Pegmode/3D-Hologram---NAIT-CMPE2965/docs/cmpe2965 hologram presentation slides in person versionV2.pdf

# Table-Top Hologram Display

CMPE2965 CAPTONE PROJECT BY

DANIEL CHU, KADEN SPARROW

# Introduction

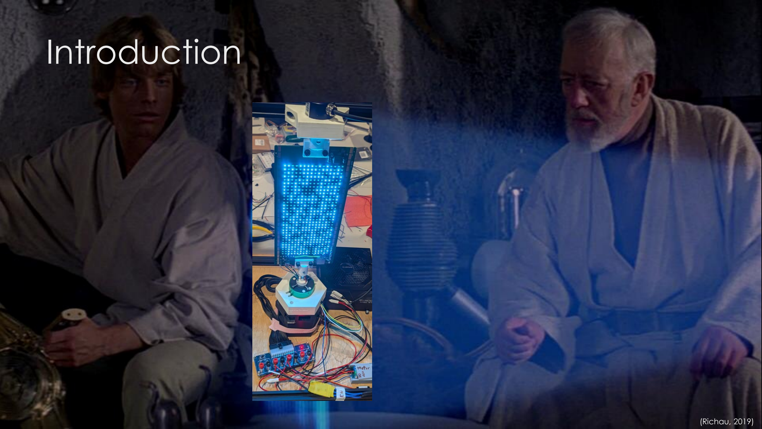
[picture p2: page 2]

(Richau, 2019)

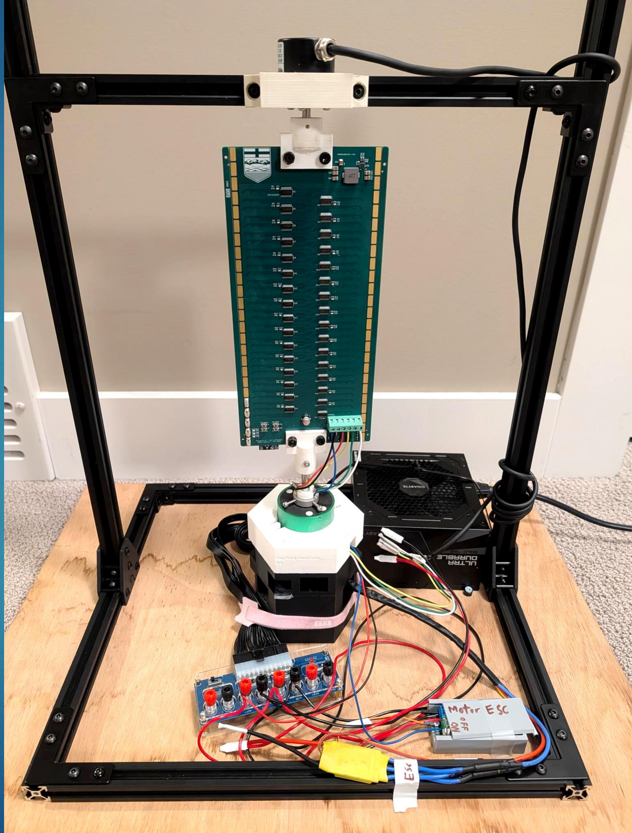
[picture p3: figure]

# Outline

- Embedded hardware
- Electro/Mechanical hardware
- Embedded software
- Server software
- Challenges
- Results

# Embedded Hardware Rotating

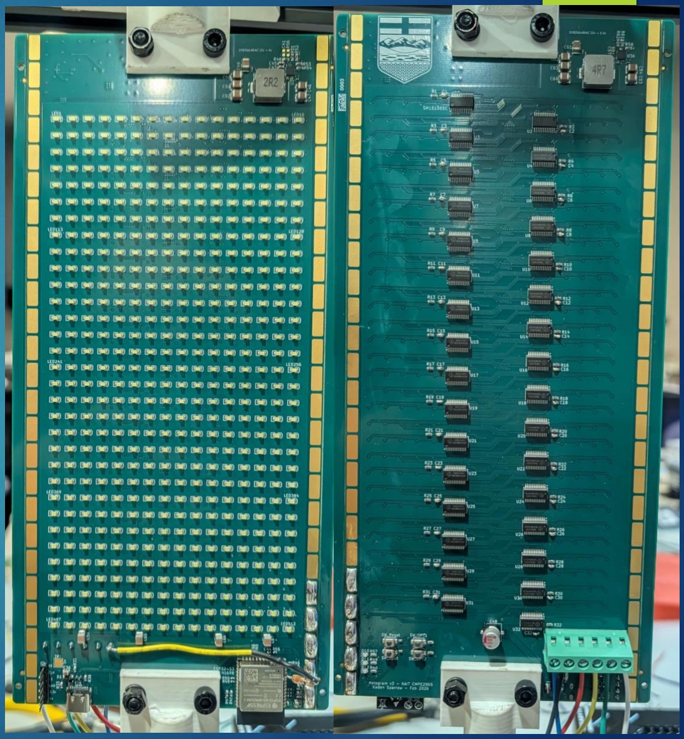
[picture p4: figure]

# Display PCB

- ESP32-S3-WROOM-1(N16R8)
- 32 x 16 LED array (512 total)
- Debug and brightness control buttons
- Debug LEDs (separate from array)
- Pads for soldering on counterweight
- Resettable fuse

# Electrical/Mechanical

# Components

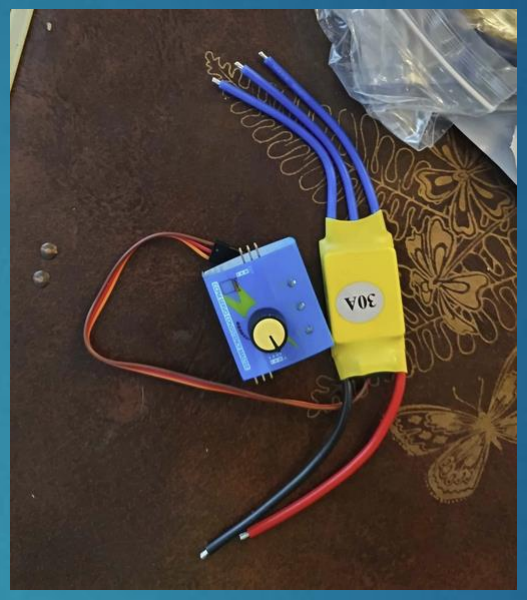
[picture p5: figure]
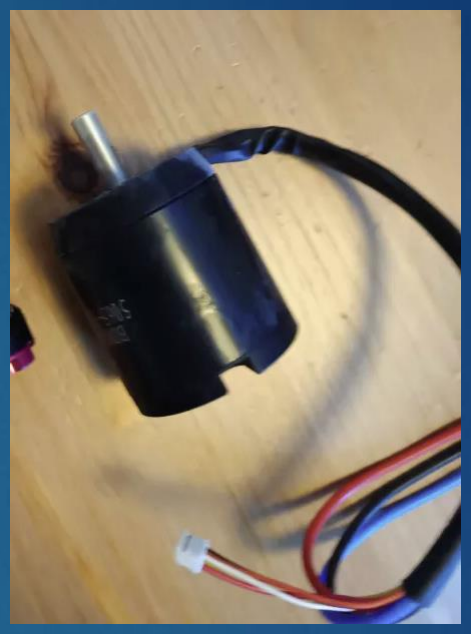
[picture p6: figure]

- 12V Electronic speed controller
- 330KV brushless motor
- 6-Wire slip ring
- Incremental rotary encoder

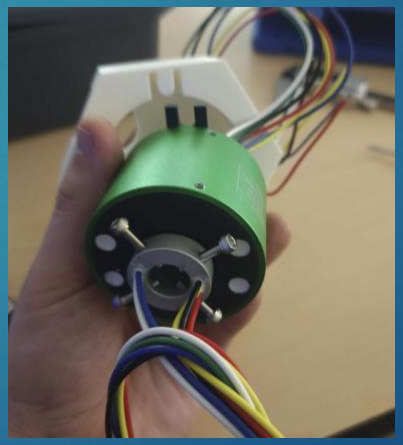
[picture p7: figure]
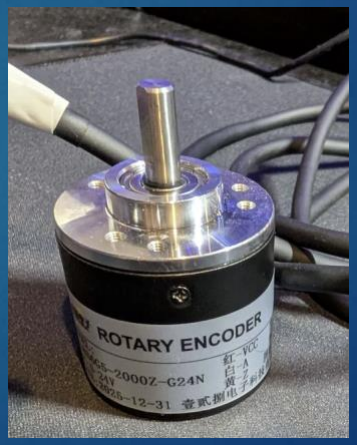
[picture p8: figure]

- Modular ATX power supply

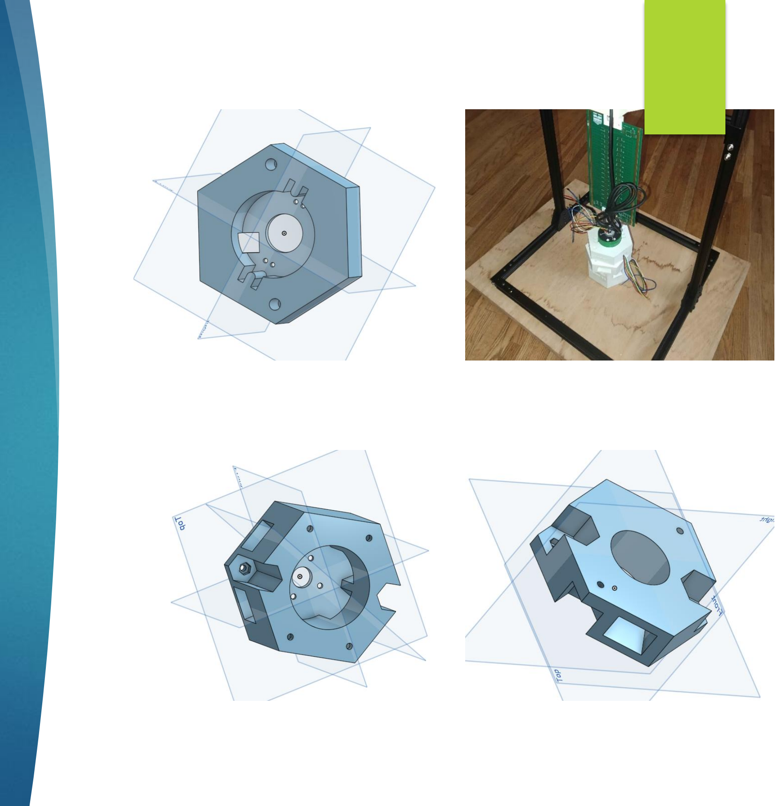
[picture p9: figure]

# Structural

# Components

- 3D printed parts to mount mechanical components
- 2020 T-Slot Aluminum
extrusions and a plywood
base as a structural frame
- All 3D printed components designed in Onshape

# Wireless control

- linear_index = (frame_index * slice_count) + slice_index;

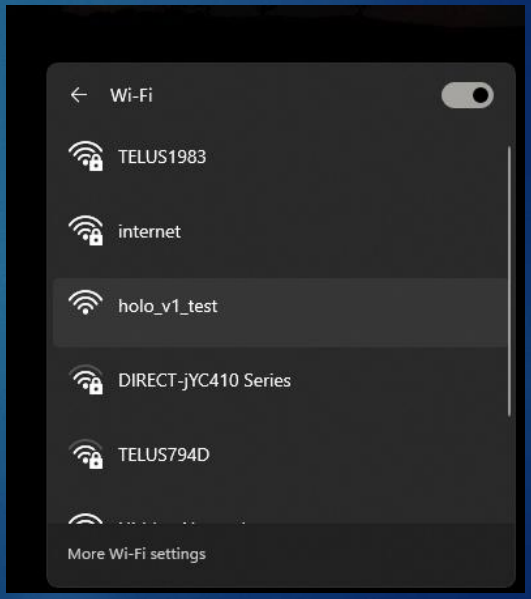
[picture p10: figure]
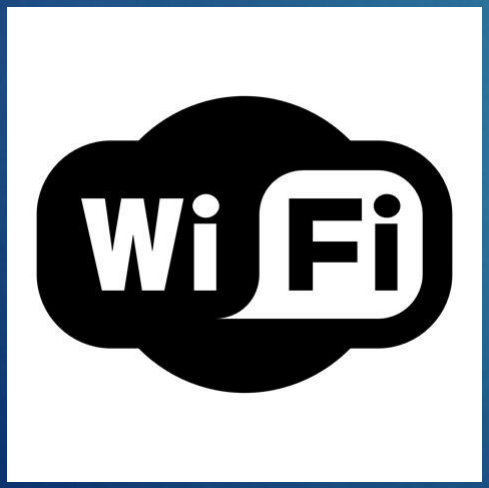
[picture p11: figure]
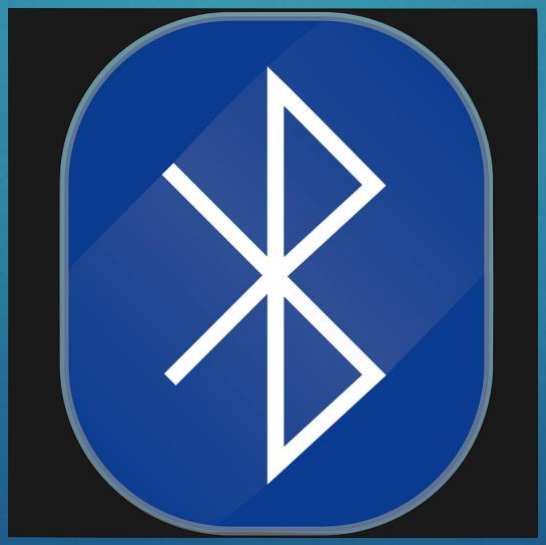
[picture p12: figure]

# Timing the Display

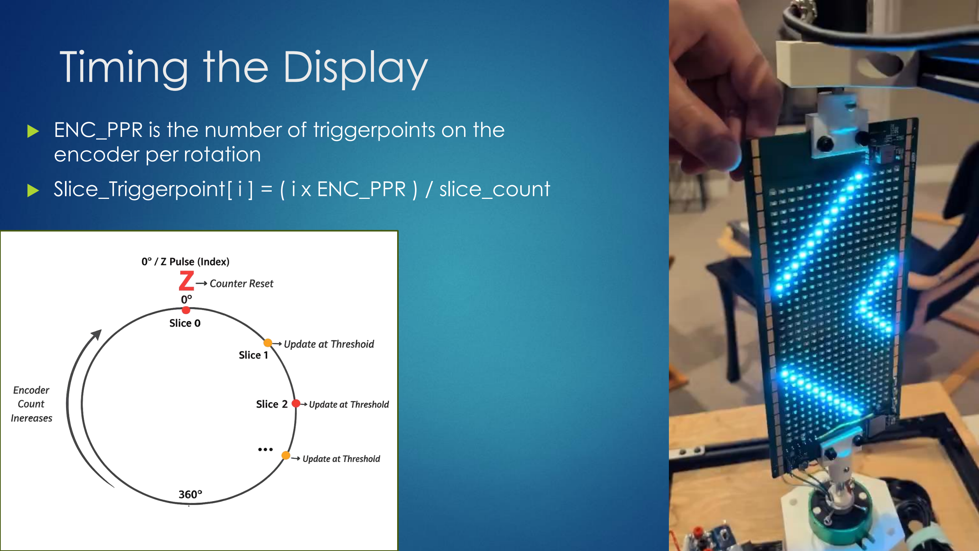
[picture p13: page 8]

- ENC_PPR is the number of triggerpoints on the encoder per rotation
- Slice_Triggerpoint[ i ] = ( i x ENC_PPR ) / slice_count

# Voxel Conversion Tool

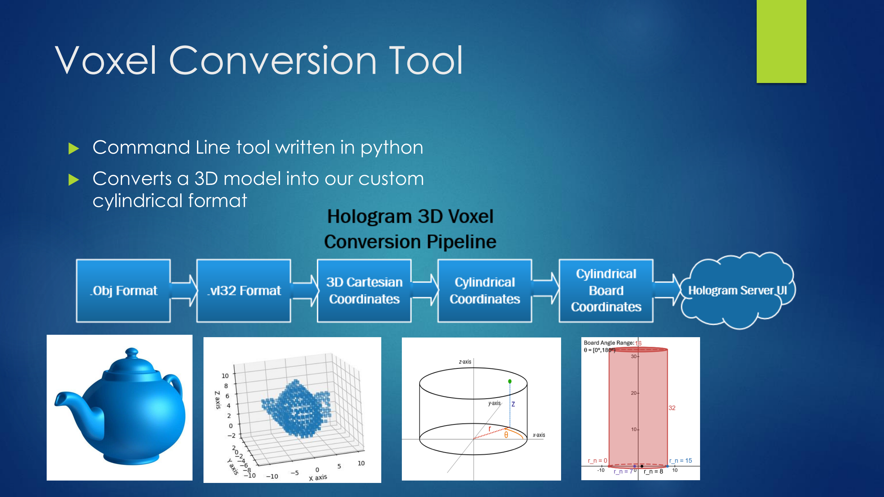
[picture p14: page 9]

- Command Line tool written in python
- Converts a 3D model into our custom cylindrical format

# Server UI

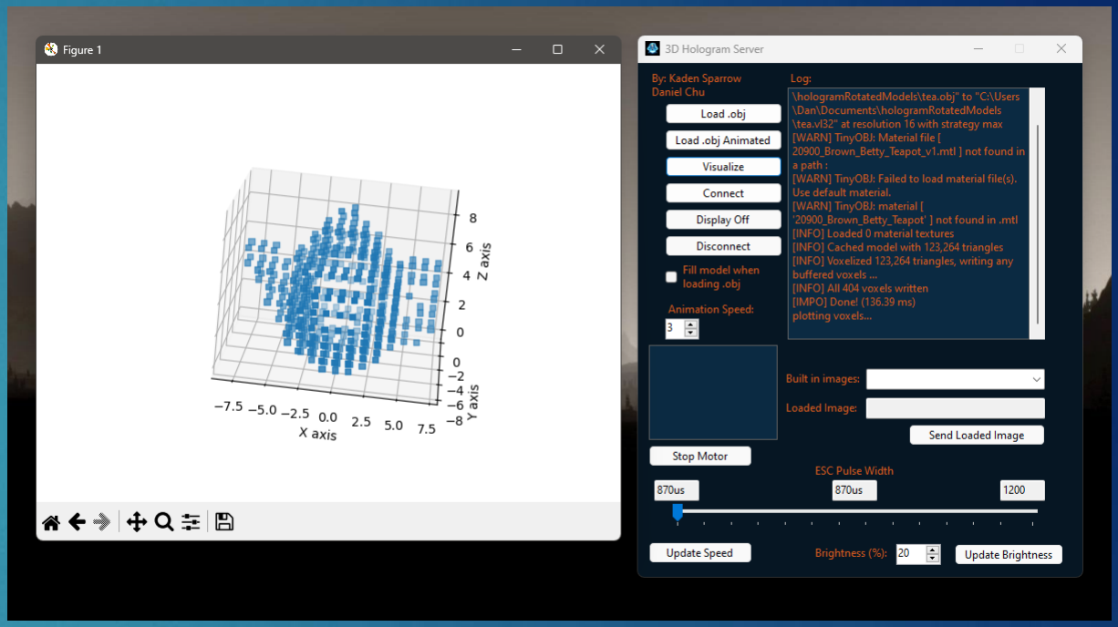
[picture p15: figure]

- WinForms application written in .NET 8
- Is the primary interface a user controls the Hologram from
- Communicates with the voxel conversion tool with Windows named pipes
- Communicates wirelessly with the microcontroller via TCP sockets over Wi-Fi

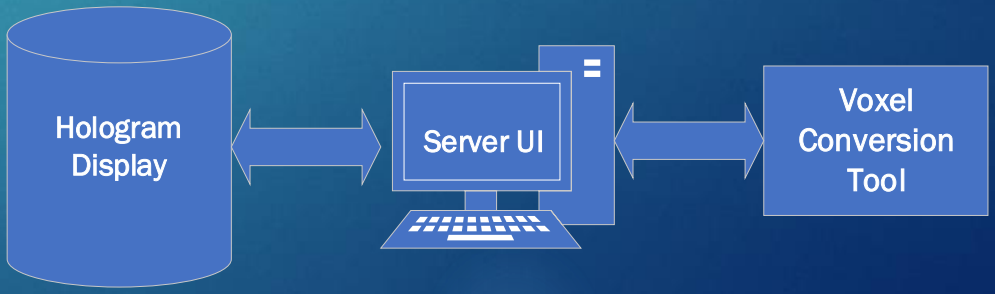
[picture p16: figure]
Hologram Display; Voxel Conversion Tool; Server UI

- Voxel conversion tool and display hardware feedback information is displayed

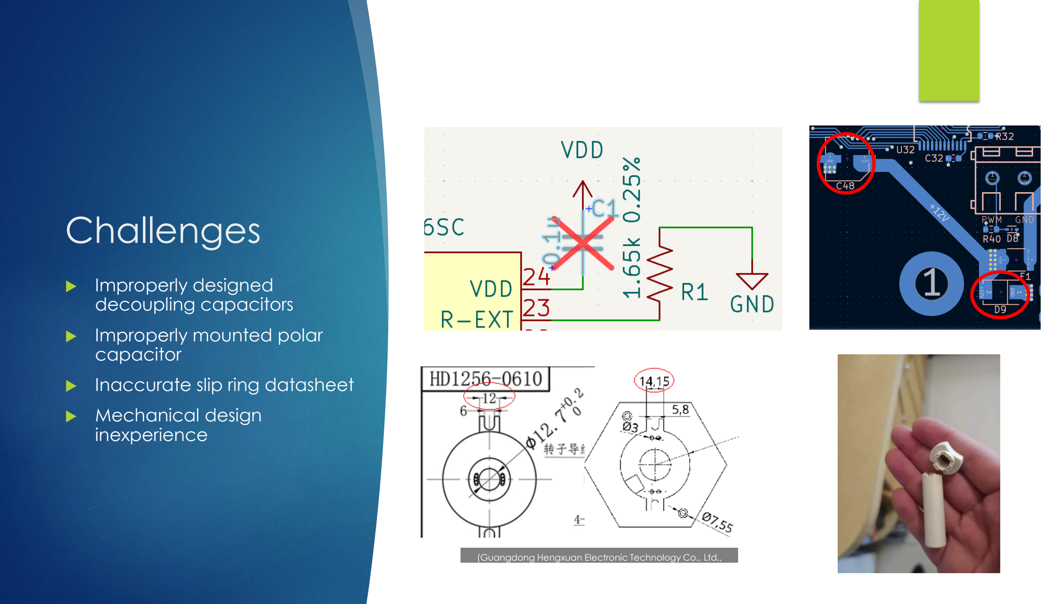
[picture p17: page 11]

## Challenges

- Improperly designed
decoupling capacitors
- Improperly mounted polar capacitor
- Inaccurate slip ring datasheet
- Mechanical design
inexperience

(Guangdong Hengxuan Electronic Technology Co., Ltd., N/A)

# Results

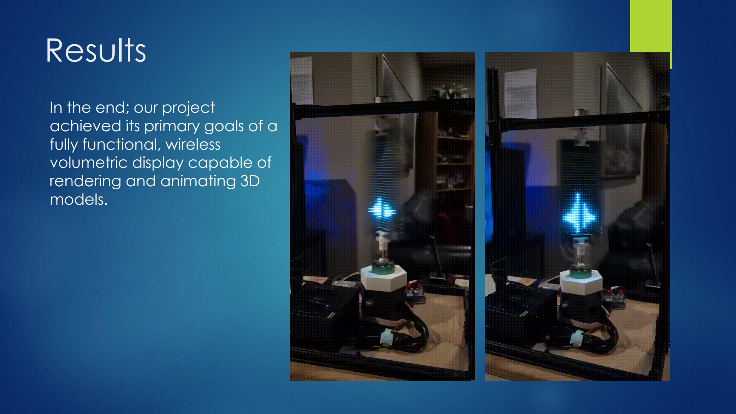
[picture p18: page 12]

In the end; our project
achieved its primary goals of a fully functional, wireless volumetric display capable of rendering and animating 3D models.

# Possible Future Improvements

- Higher resolution color display
- Faster conversion pipeline
- Custom 3D model voxelizer
- Web UI

# Thank you!

- References
- Richau, A. (2019, September 20). 6 ways holograms play an important role in Star Wars storytelling. StarWars.com. https://www.starwars.com/news/6-ways-holograms-play-an-important-role (https://www.starwars.com/news/6-ways-holograms-play-an-important-role-in-star-wars)- (https://www.starwars.com/news/6-ways-holograms-play-an-important-role-in-star-wars)in (https://www.starwars.com/news/6-ways-holograms-play-an-important-role-in-star-wars)- (https://www.starwars.com/news/6-ways-holograms-play-an-important-role-in-star-wars)star (https://www.starwars.com/news/6-ways-holograms-play-an-important-role-in-star-wars)- (https://www.starwars.com/news/6-ways-holograms-play-an-important-role-in-star-wars)wars (https://www.starwars.com/news/6-ways-holograms-play-an-important-role-in-star-wars)
- Guangdong Hengxuan Electronic Technology Co., Ltd. (N/A). HD1256-0610 Slip ring Datasheet. Retrieved from https://www.alibaba.com/product-detail/Conductive-Slip-Ring-12-7mm (https://www.alibaba.com/product-detail/Conductive-Slip-Ring-12-7mm-Bore_1600974440492.html)- (https://www.alibaba.com/product-detail/Conductive-Slip-Ring-12-7mm-Bore_1600974440492.html)Bore_1600974440492.html (https://www.alibaba.com/product-detail/Conductive-Slip-Ring-12-7mm-Bore_1600974440492.html)

# Questions?

# Embedded Hardware

# Problems and Fixes

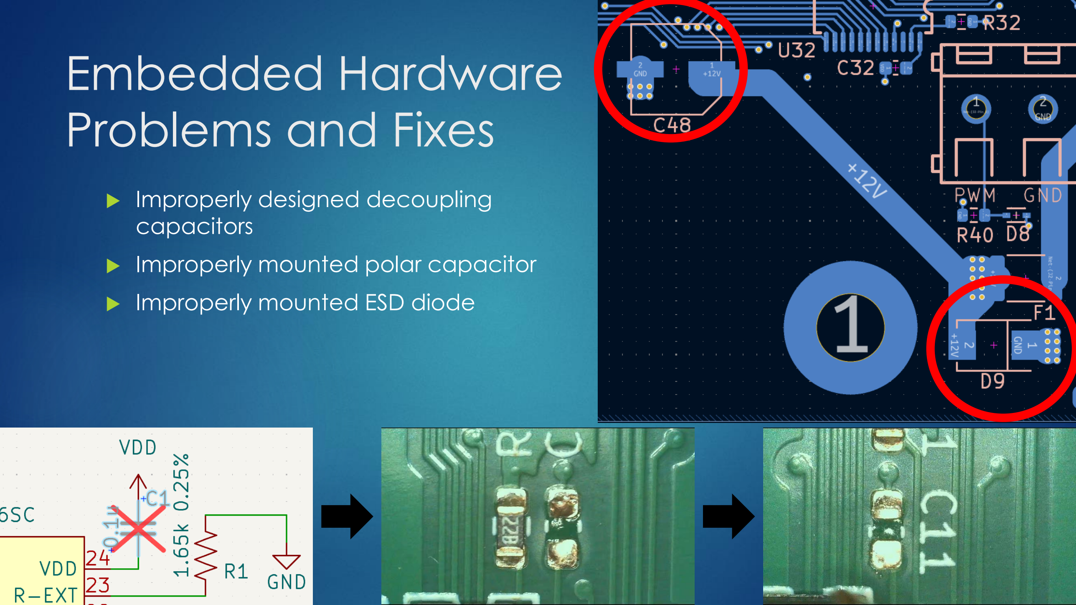
[picture p19: page 16]

- Improperly designed decoupling capacitors
- Improperly mounted polar capacitor
- Improperly mounted ESD diode

# 3D Print Design Issues

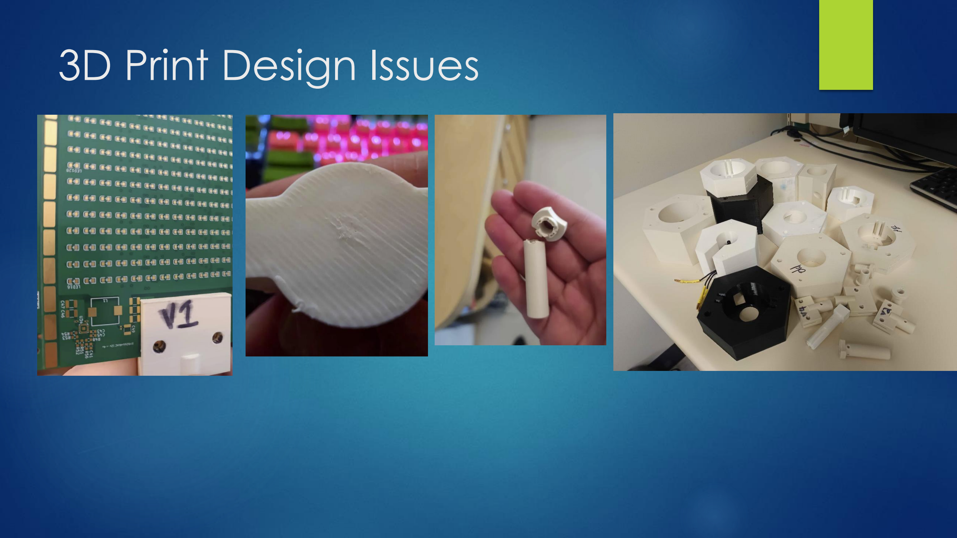
[picture p20: page 17]

# Verification tools

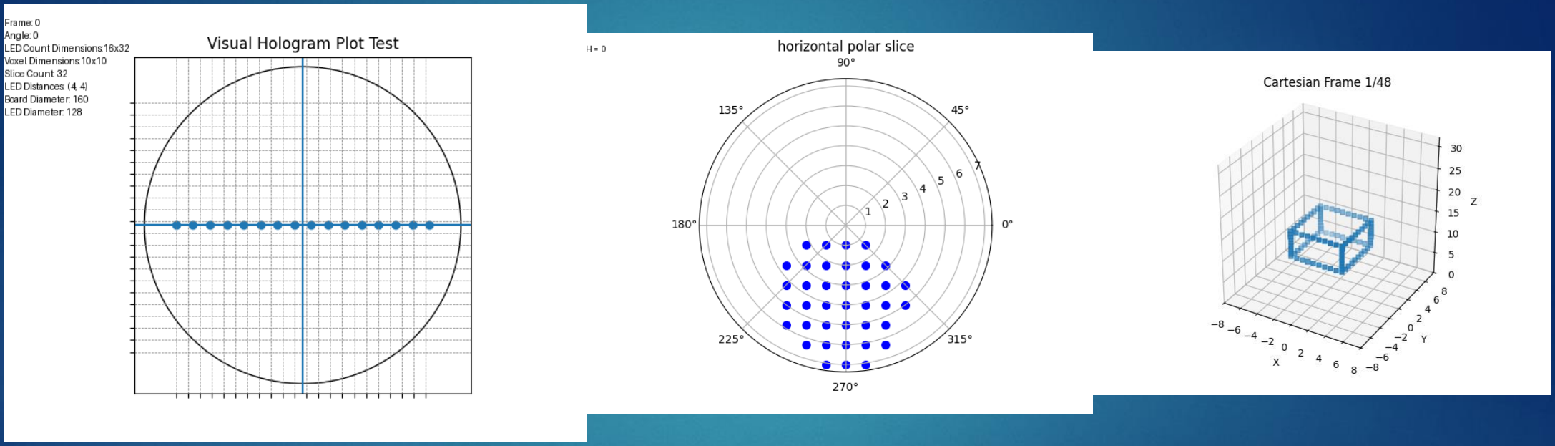
[picture p21: figure]
