Pegmode/3D-Hologram---NAIT-CMPE2965/server/tools/voxelConversion/CylindricalAnimation.gif

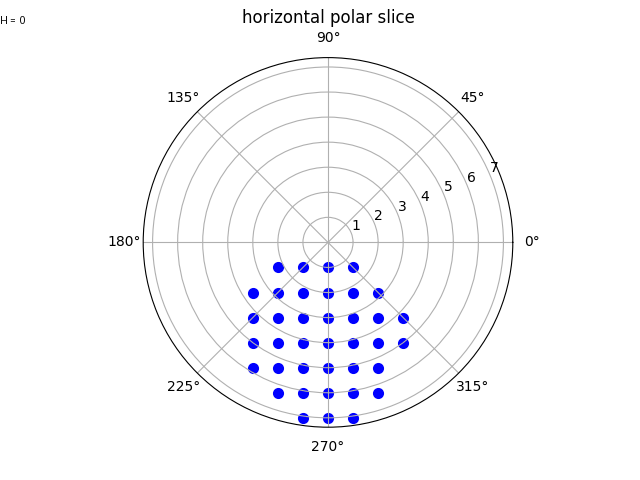
server/tools/voxelConversion/CylindricalAnimation.gif
