Pegmode/3D-Hologram---NAIT-CMPE2965/Hardware/Mechanical Parts/Datasheets/motor dimensional datasheet.png

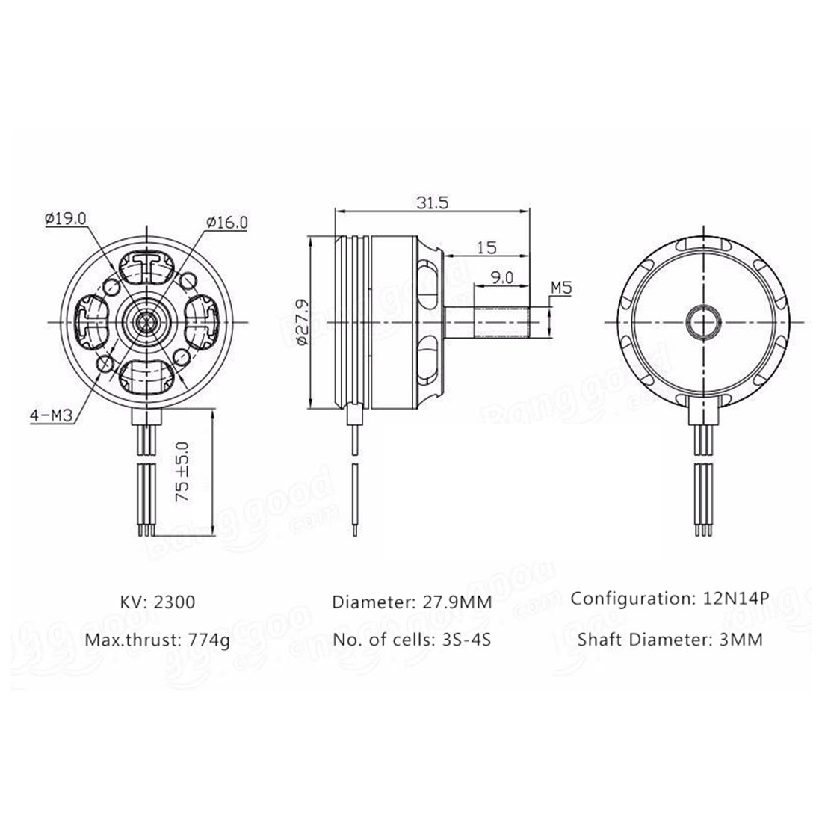
Hardware/Mechanical Parts/Datasheets/motor dimensional datasheet.png
