Pegmode/3D-Hologram---NAIT-CMPE2965/Hardware/Mechanical Parts/Datasheets/slipring dimensional datasheet.png

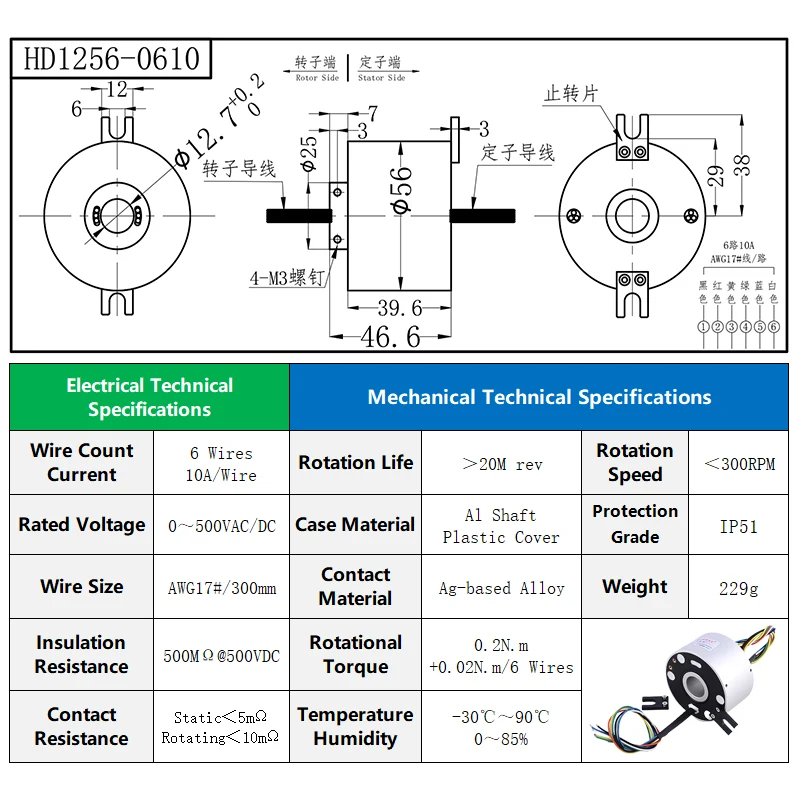
Hardware/Mechanical Parts/Datasheets/slipring dimensional datasheet.png
