Pegmode/3D-Hologram---NAIT-CMPE2965/Hardware/hologram v3/schematic photos/sm16206 setup.png

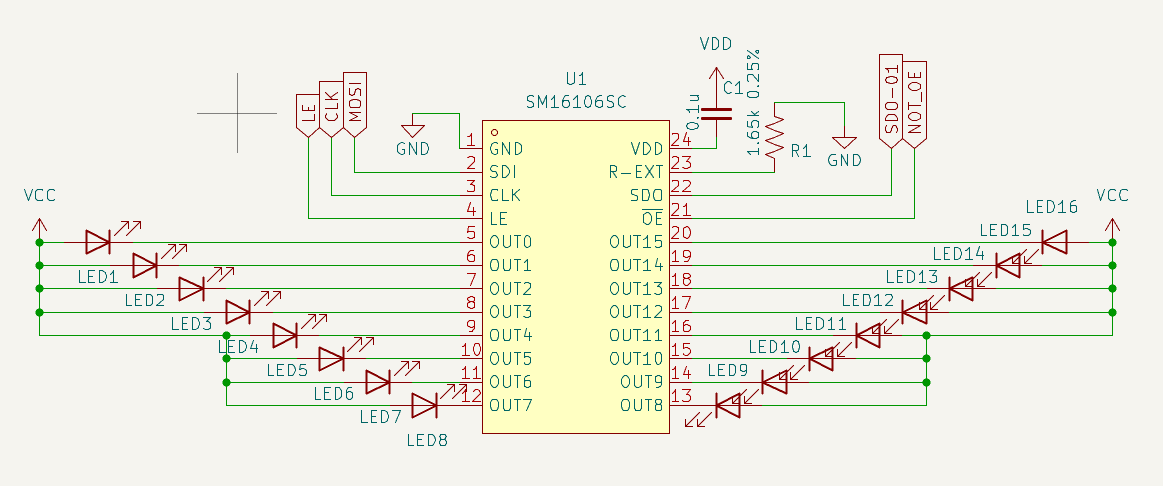
Hardware/hologram v3/schematic photos/sm16206 setup.png
