Pegmode/3D-Hologram---NAIT-CMPE2965/Hardware/Mechanical Parts/Motor Mount/Motor Mount Drawing V1.pdf

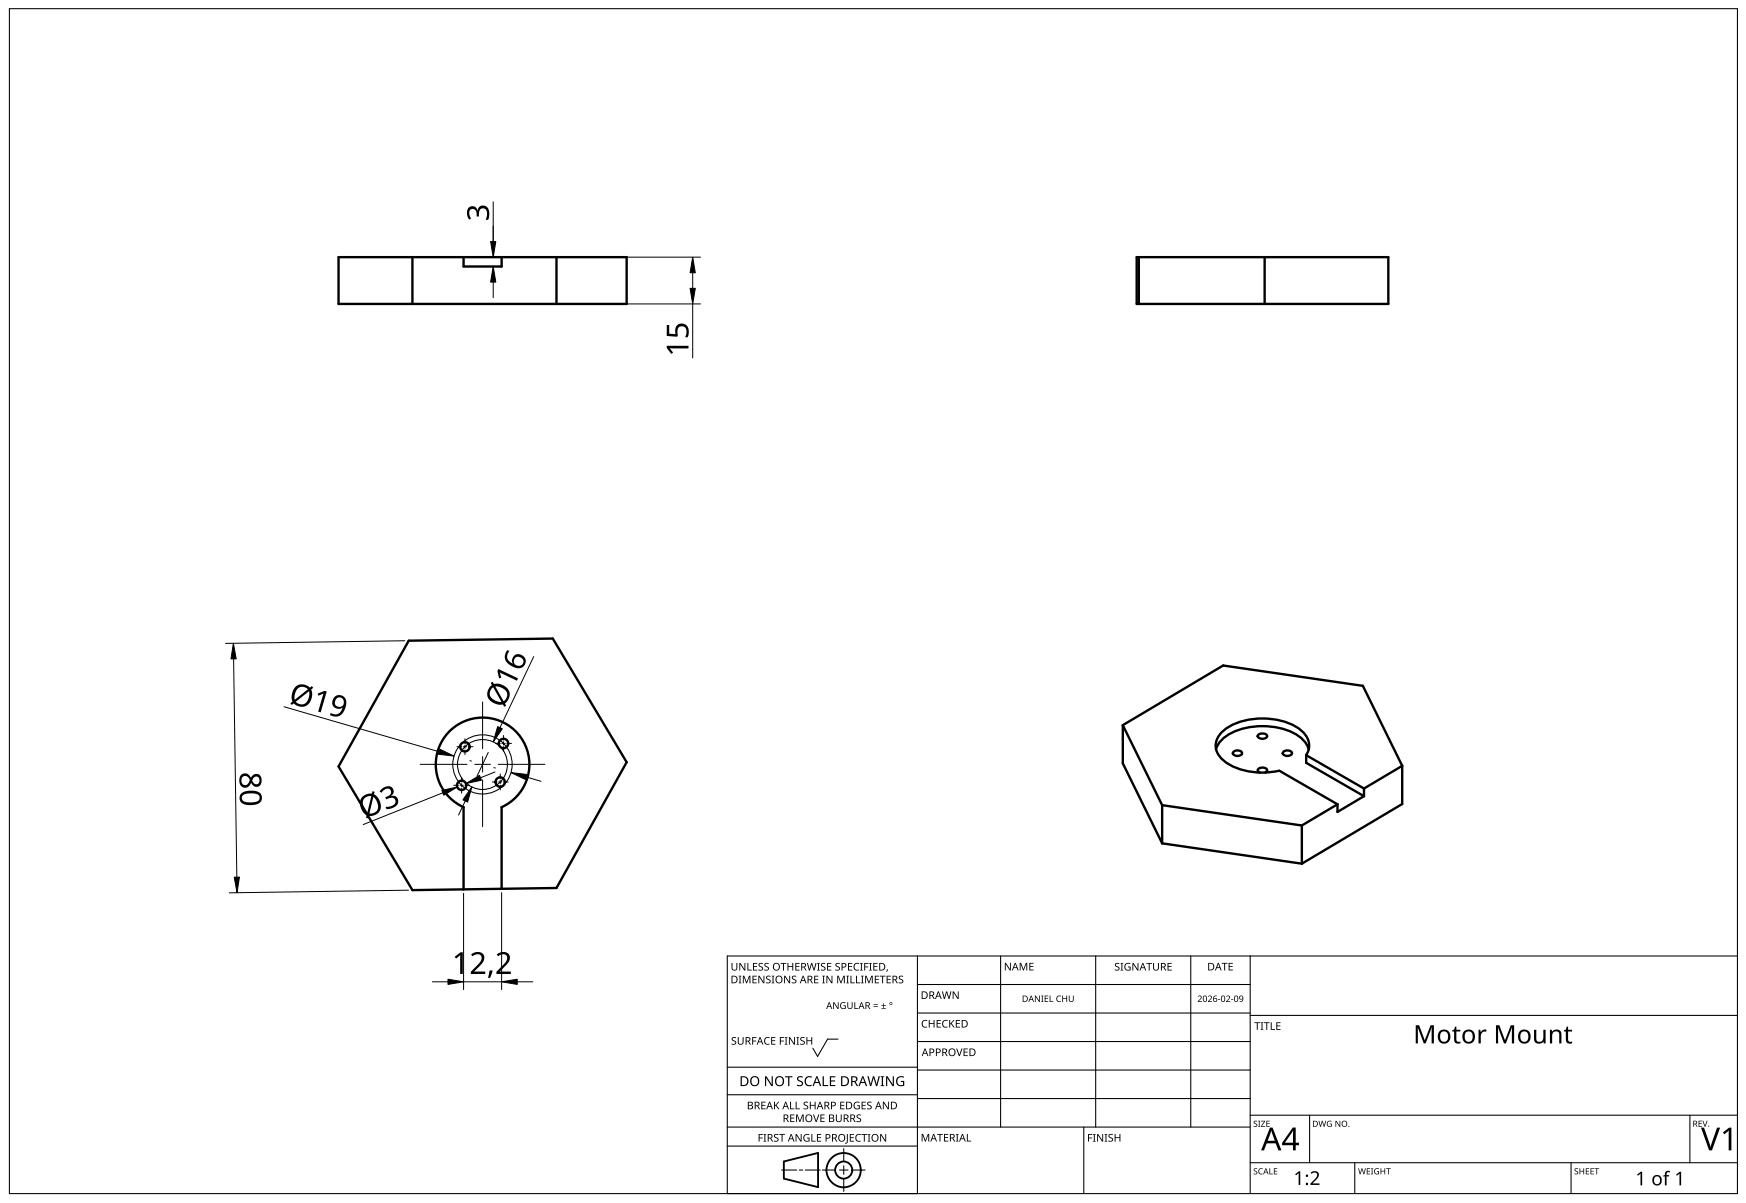
[picture p65: page 1]
