Pegmode/3D-Hologram---NAIT-CMPE2965/Hardware/Mechanical Parts/Test Parts/Test Shaft Bolt Adapter/Test Shaft Bolt Adapter.pdf

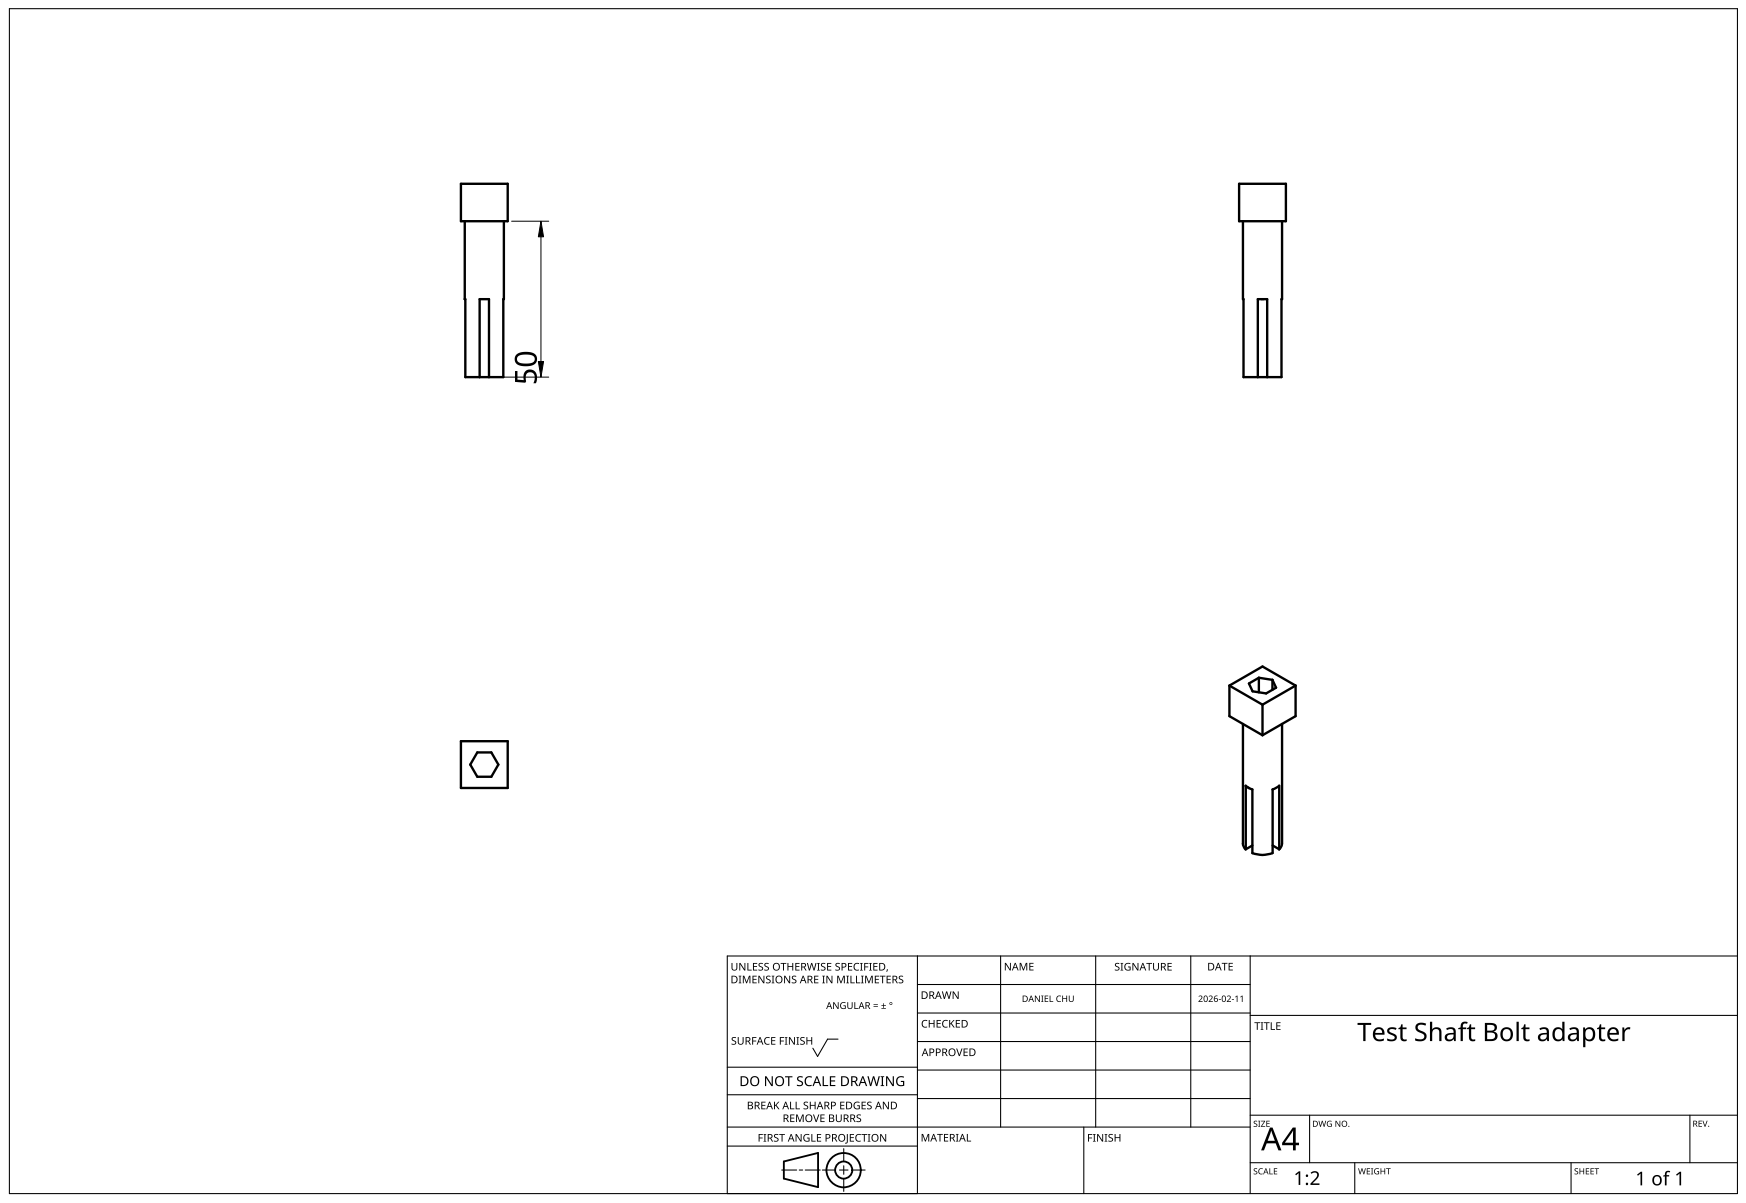
[picture p66: page 1]
