Pegmode/3D-Hologram---NAIT-CMPE2965/Hardware/Mechanical Parts/Motor Coupler Spacer/Motor Coupler Spacer Drawing V3.pdf

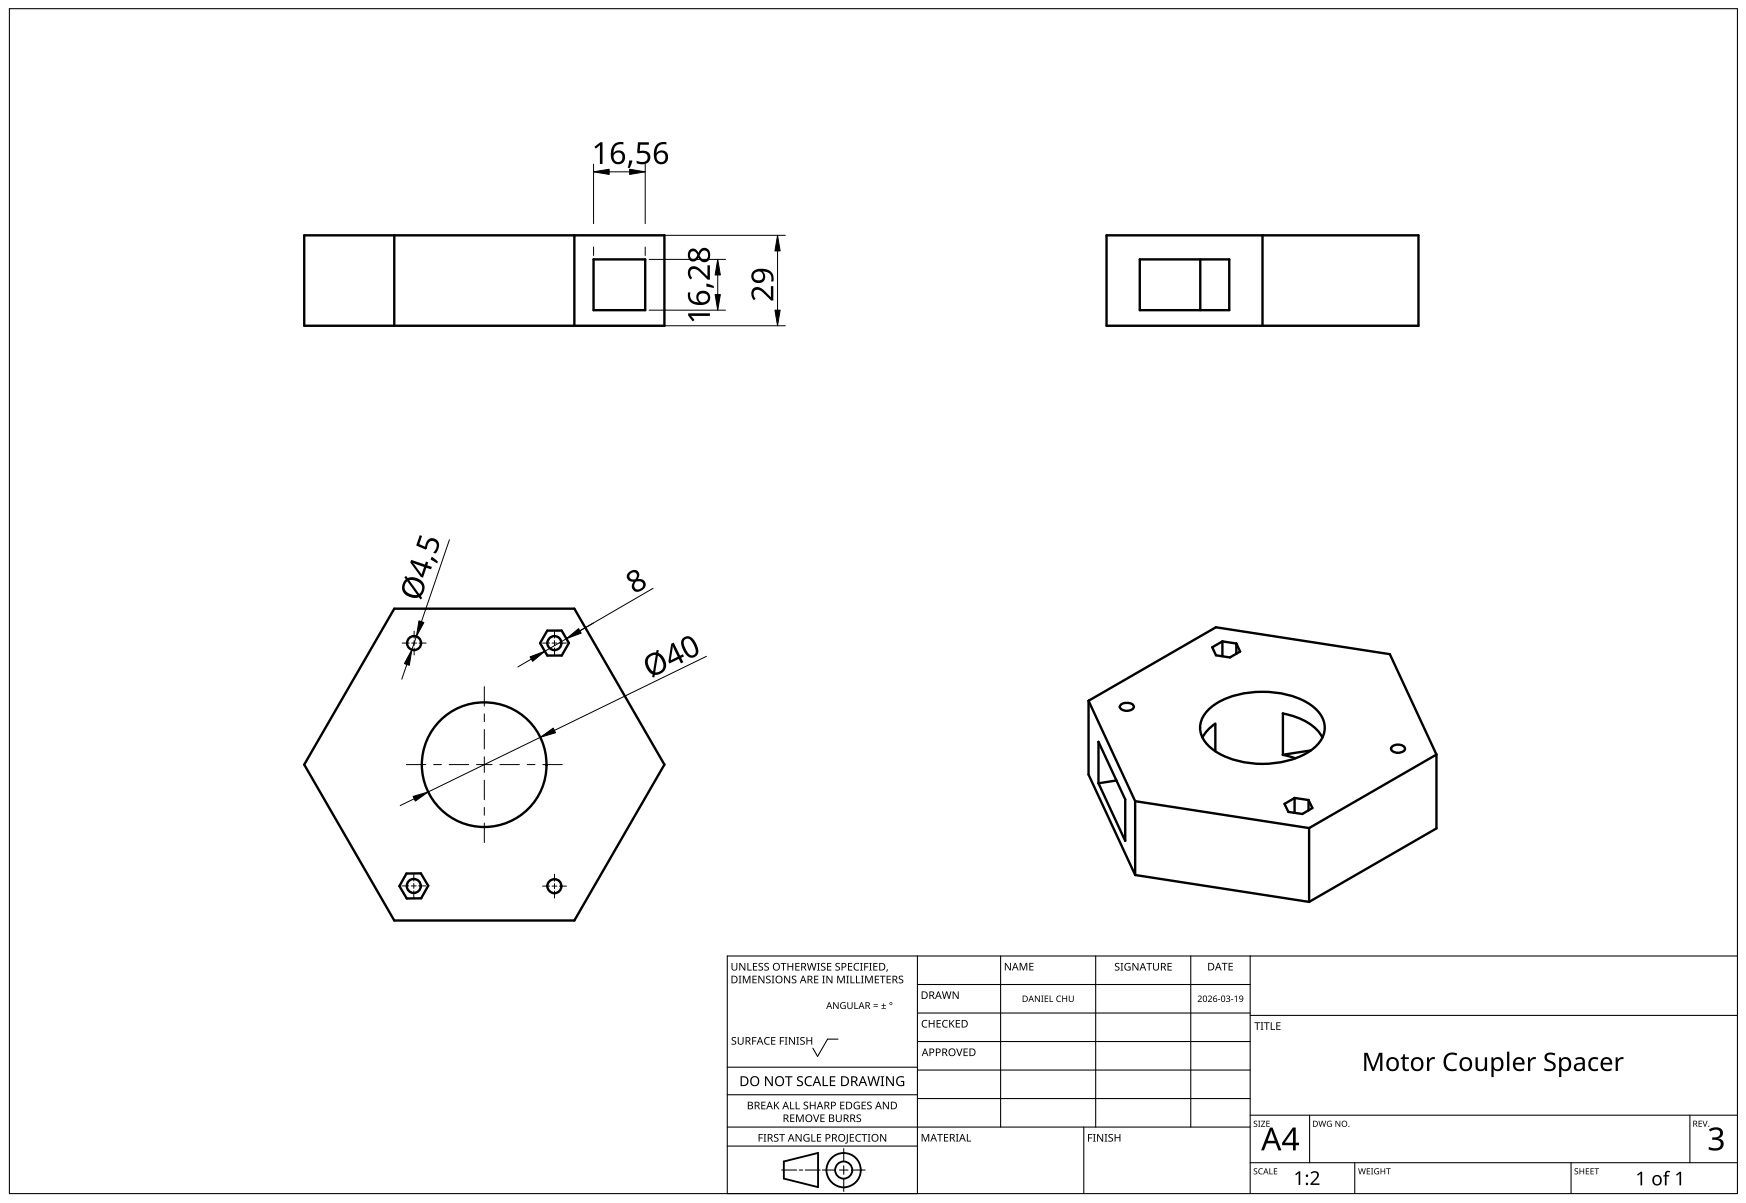
[picture p67: page 1]
