Pegmode/3D-Hologram---NAIT-CMPE2965/Hardware/Mechanical Parts/Slip Ring Shaft Adapter/Slip Ring Shaft Adapter Drawing V1.pdf

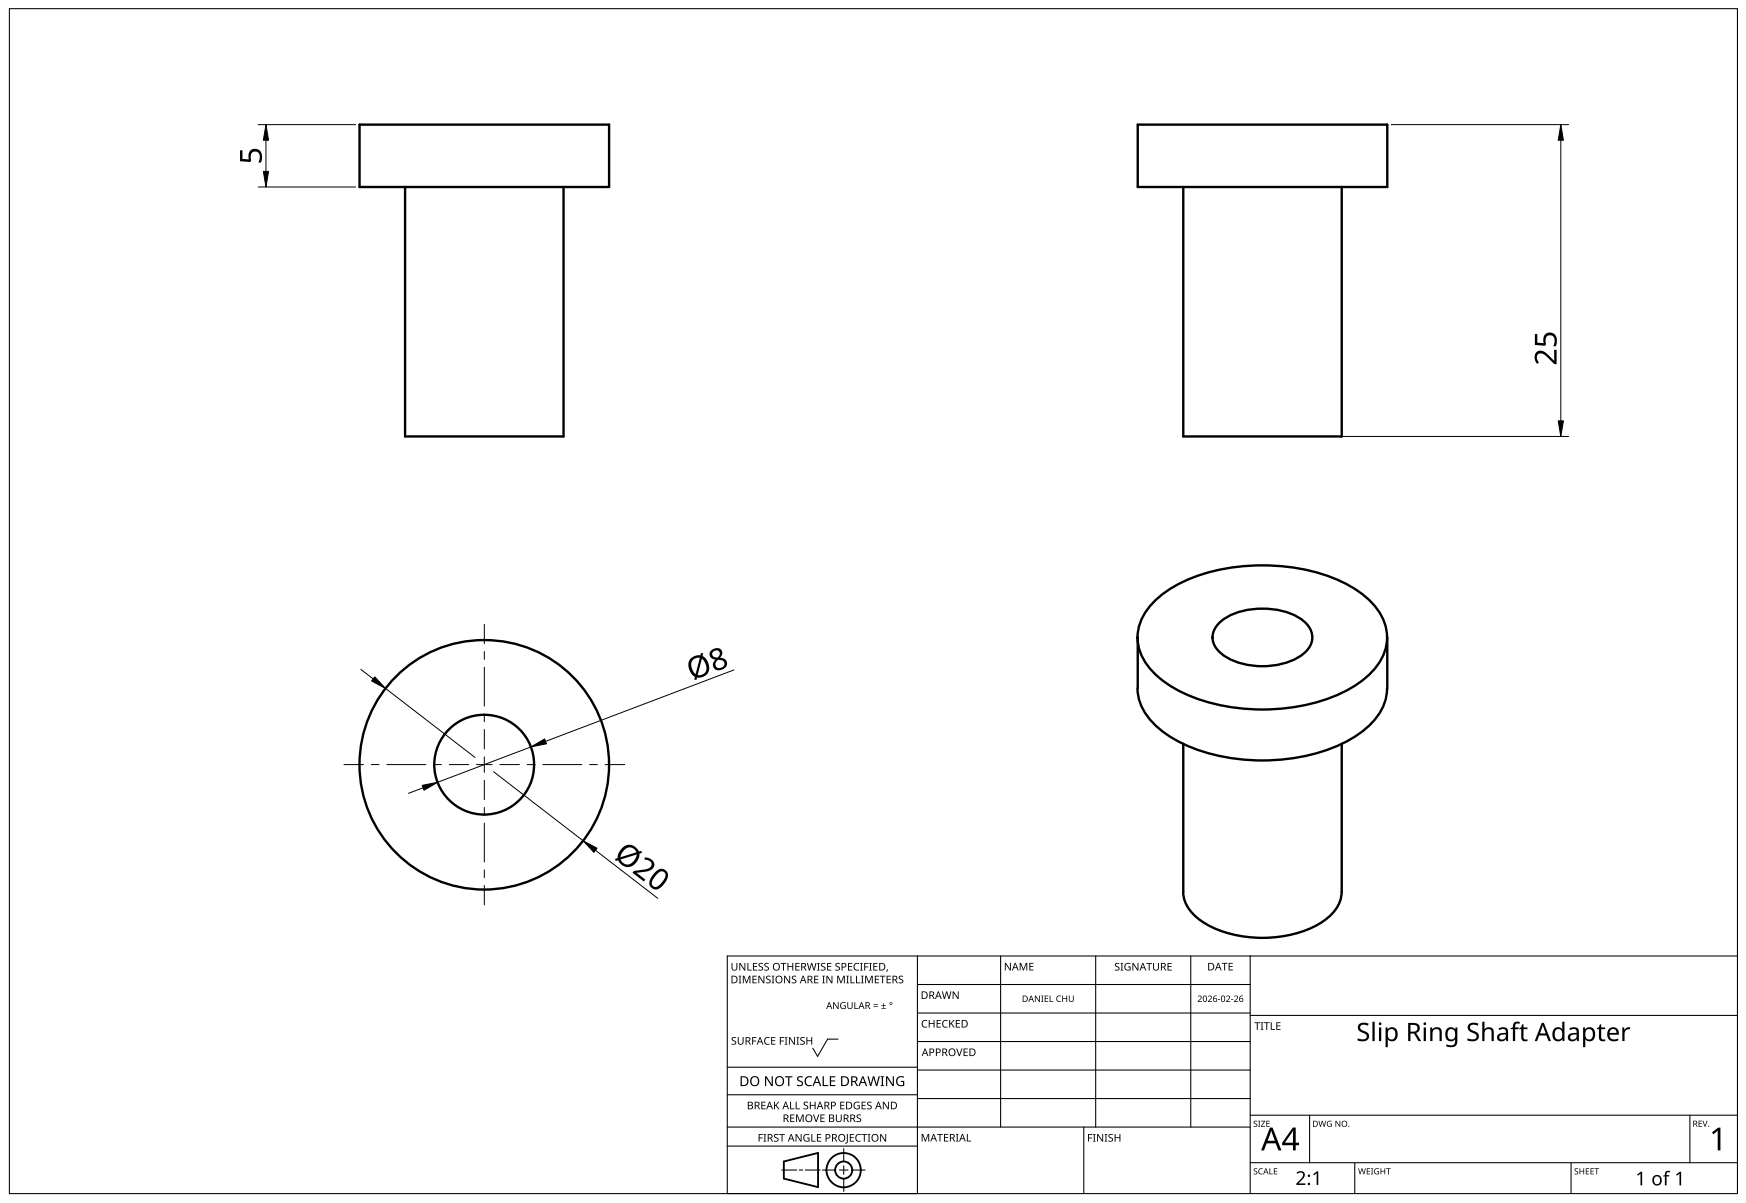
[picture p68: page 1]
