Pegmode/3D-Hologram---NAIT-CMPE2965/Hardware/Mechanical Parts/Motor Mount/SK Motor Mount Drawing V2.pdf

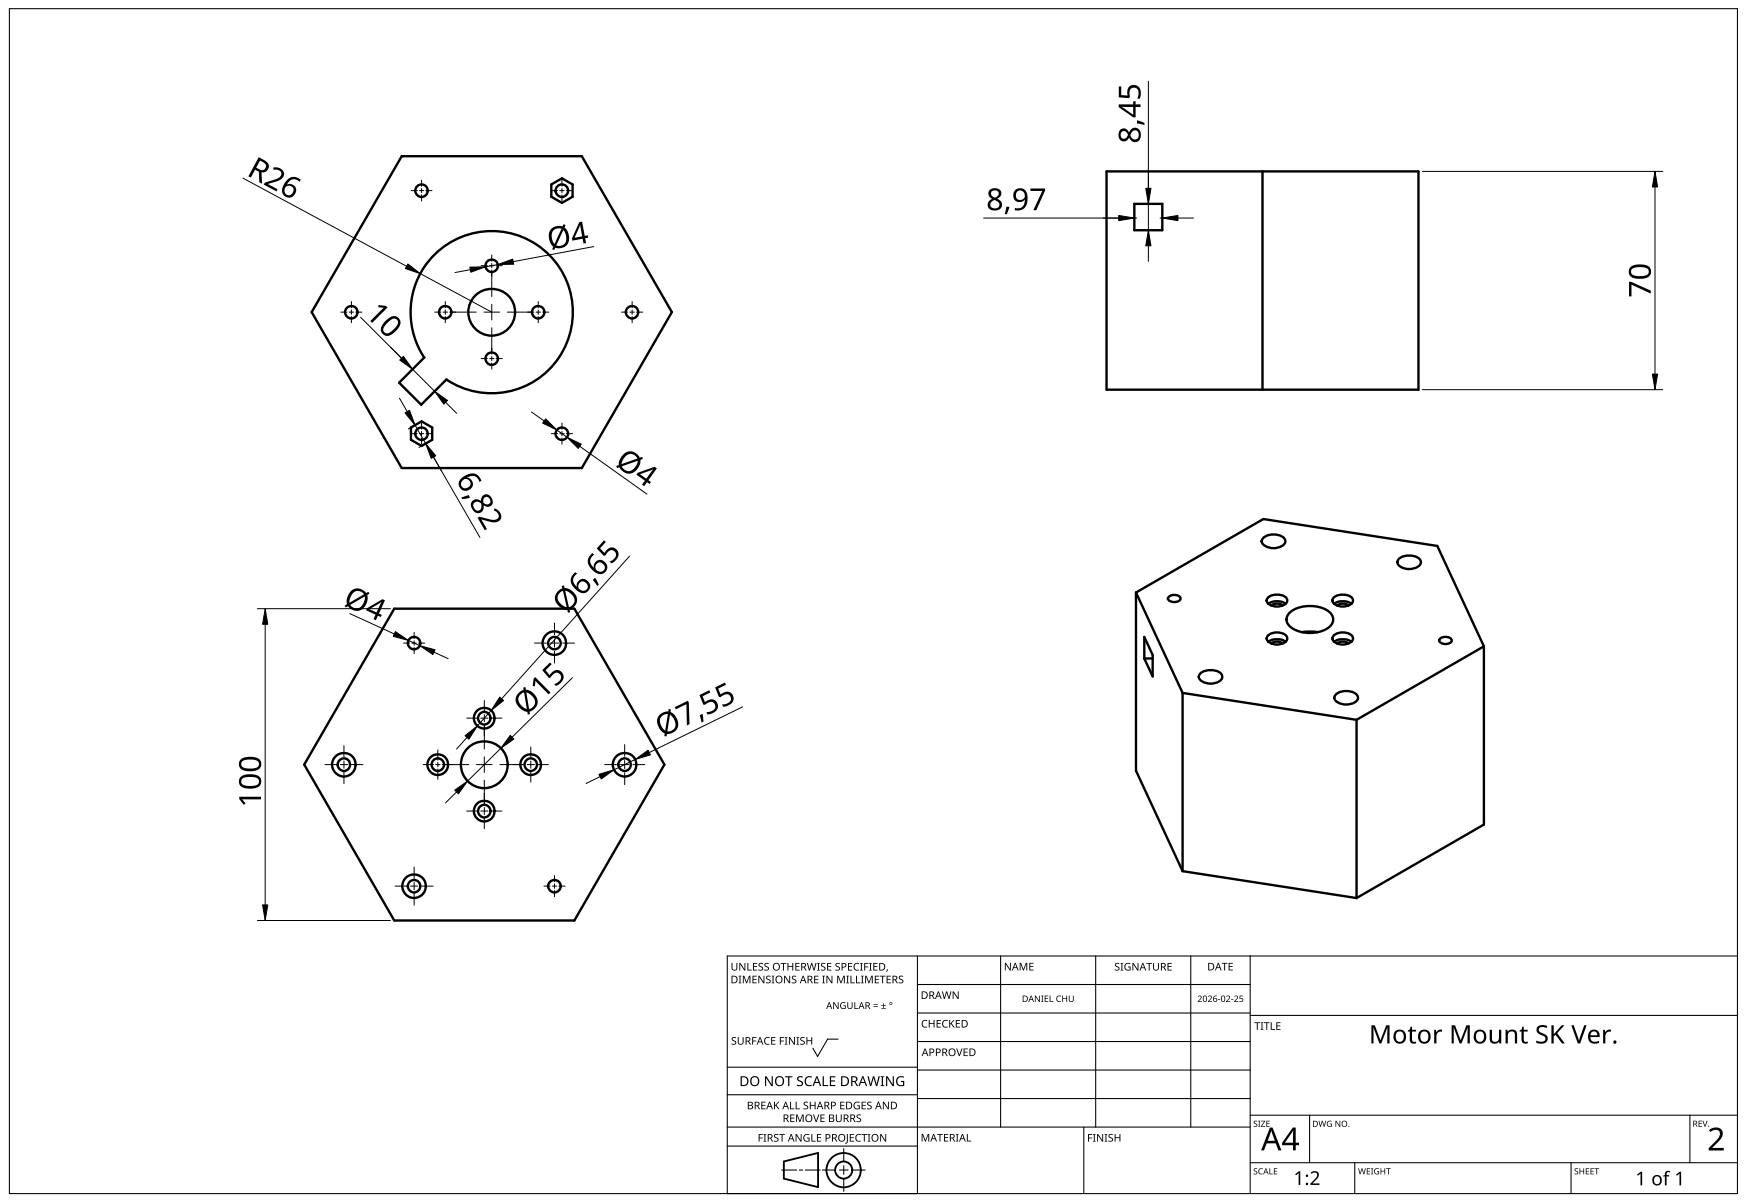
[picture p69: page 1]
