Pegmode/3D-Hologram---NAIT-CMPE2965/Hardware/Mechanical Parts/Slip Ring Connector/Slip Ring Connector Drawing V6.pdf

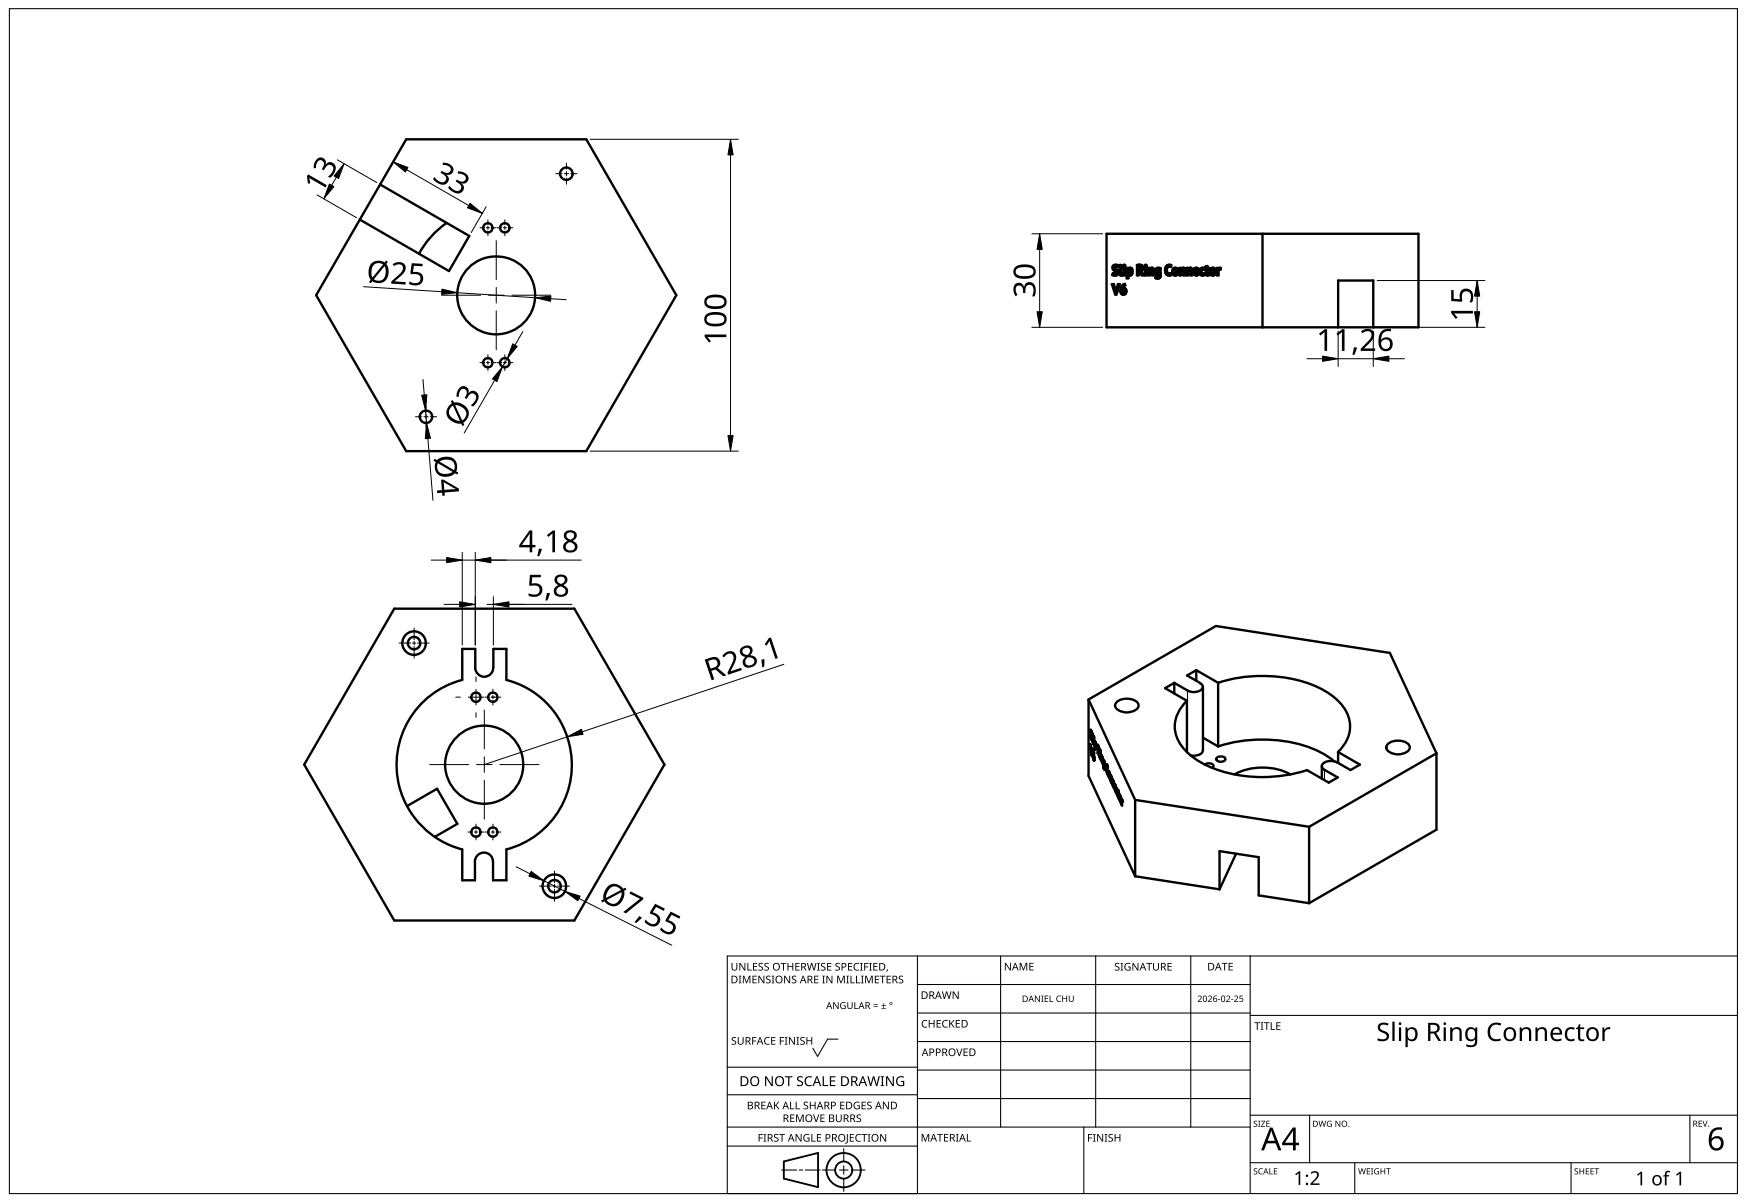
[picture p70: page 1]
