Pegmode/3D-Hologram---NAIT-CMPE2965/Hardware/Mechanical Parts/Motor Mount/SK Motor Mount Drawing V1.pdf

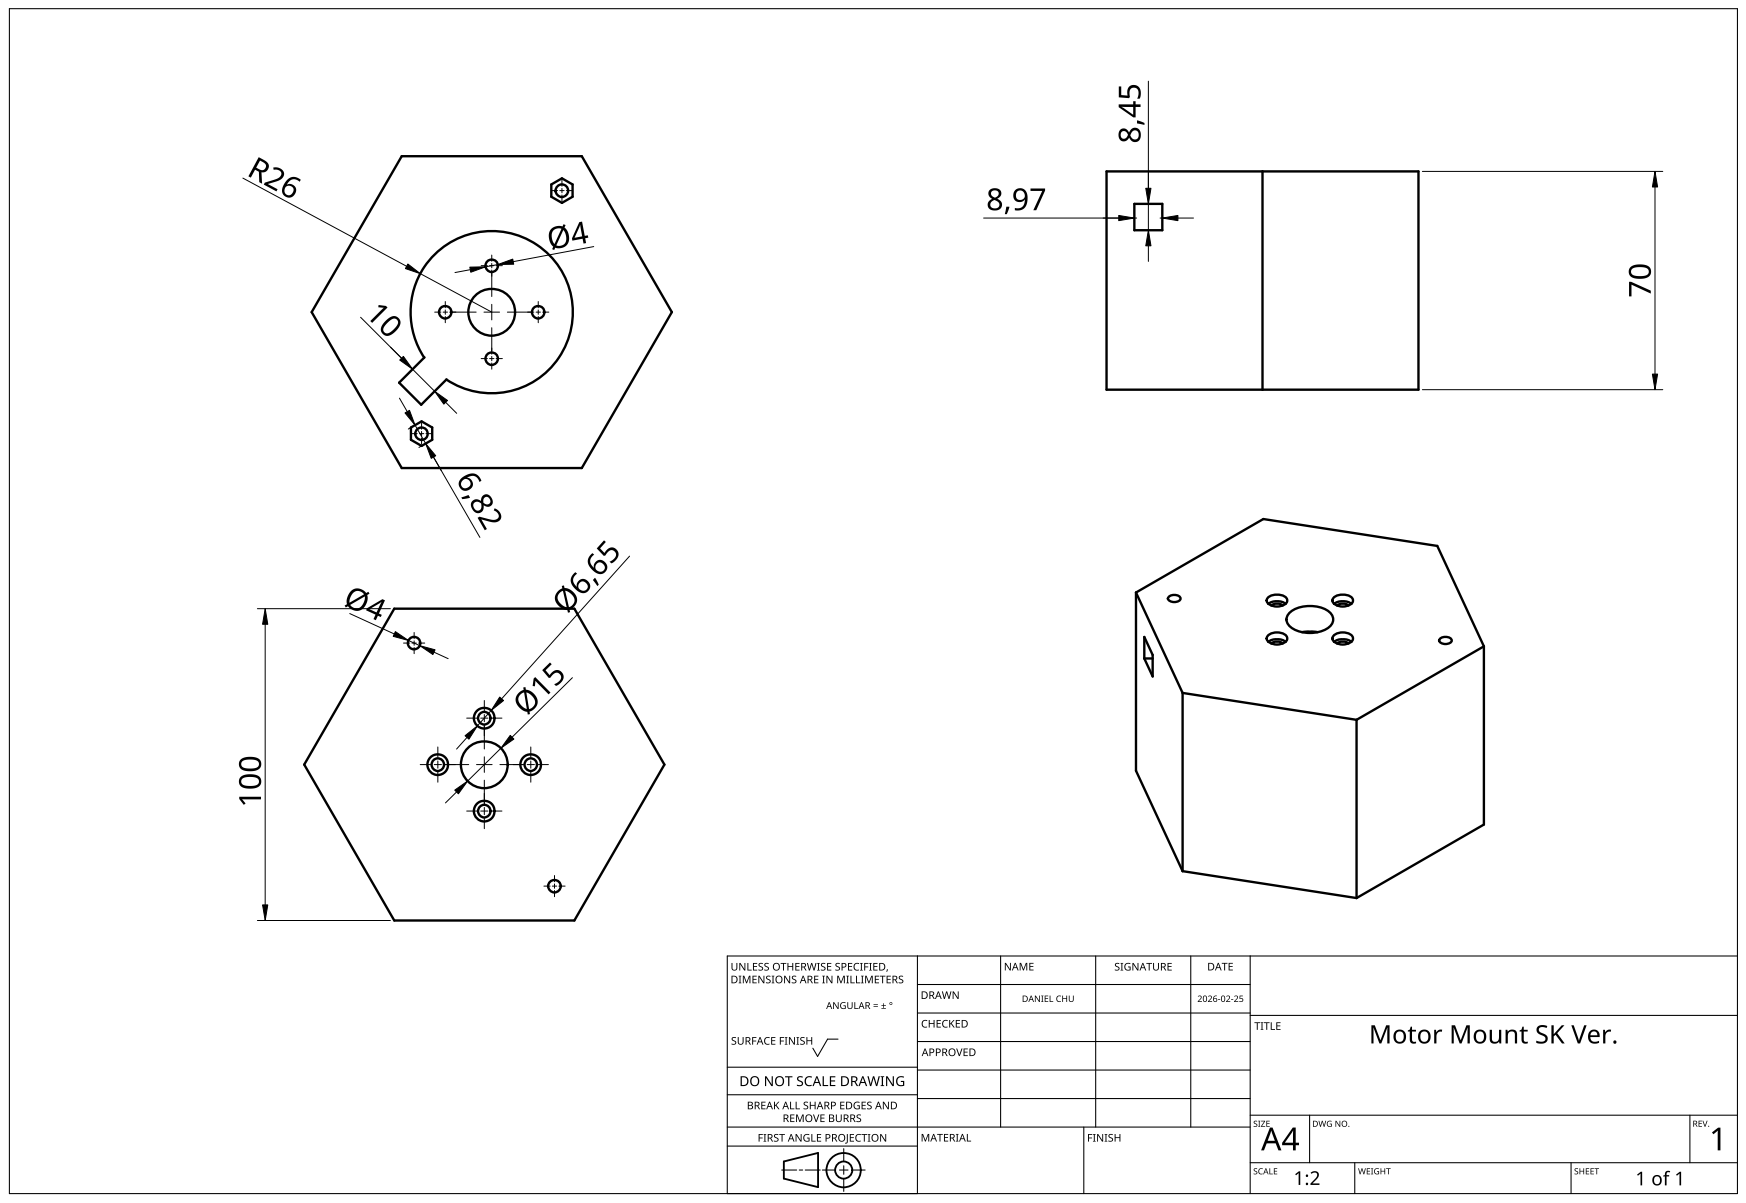
[picture p71: page 1]
