Pegmode/3D-Hologram---NAIT-CMPE2965/Hardware/Mechanical Parts/Slip Ring Connector/Slip Ring Connector Drawing V4.pdf

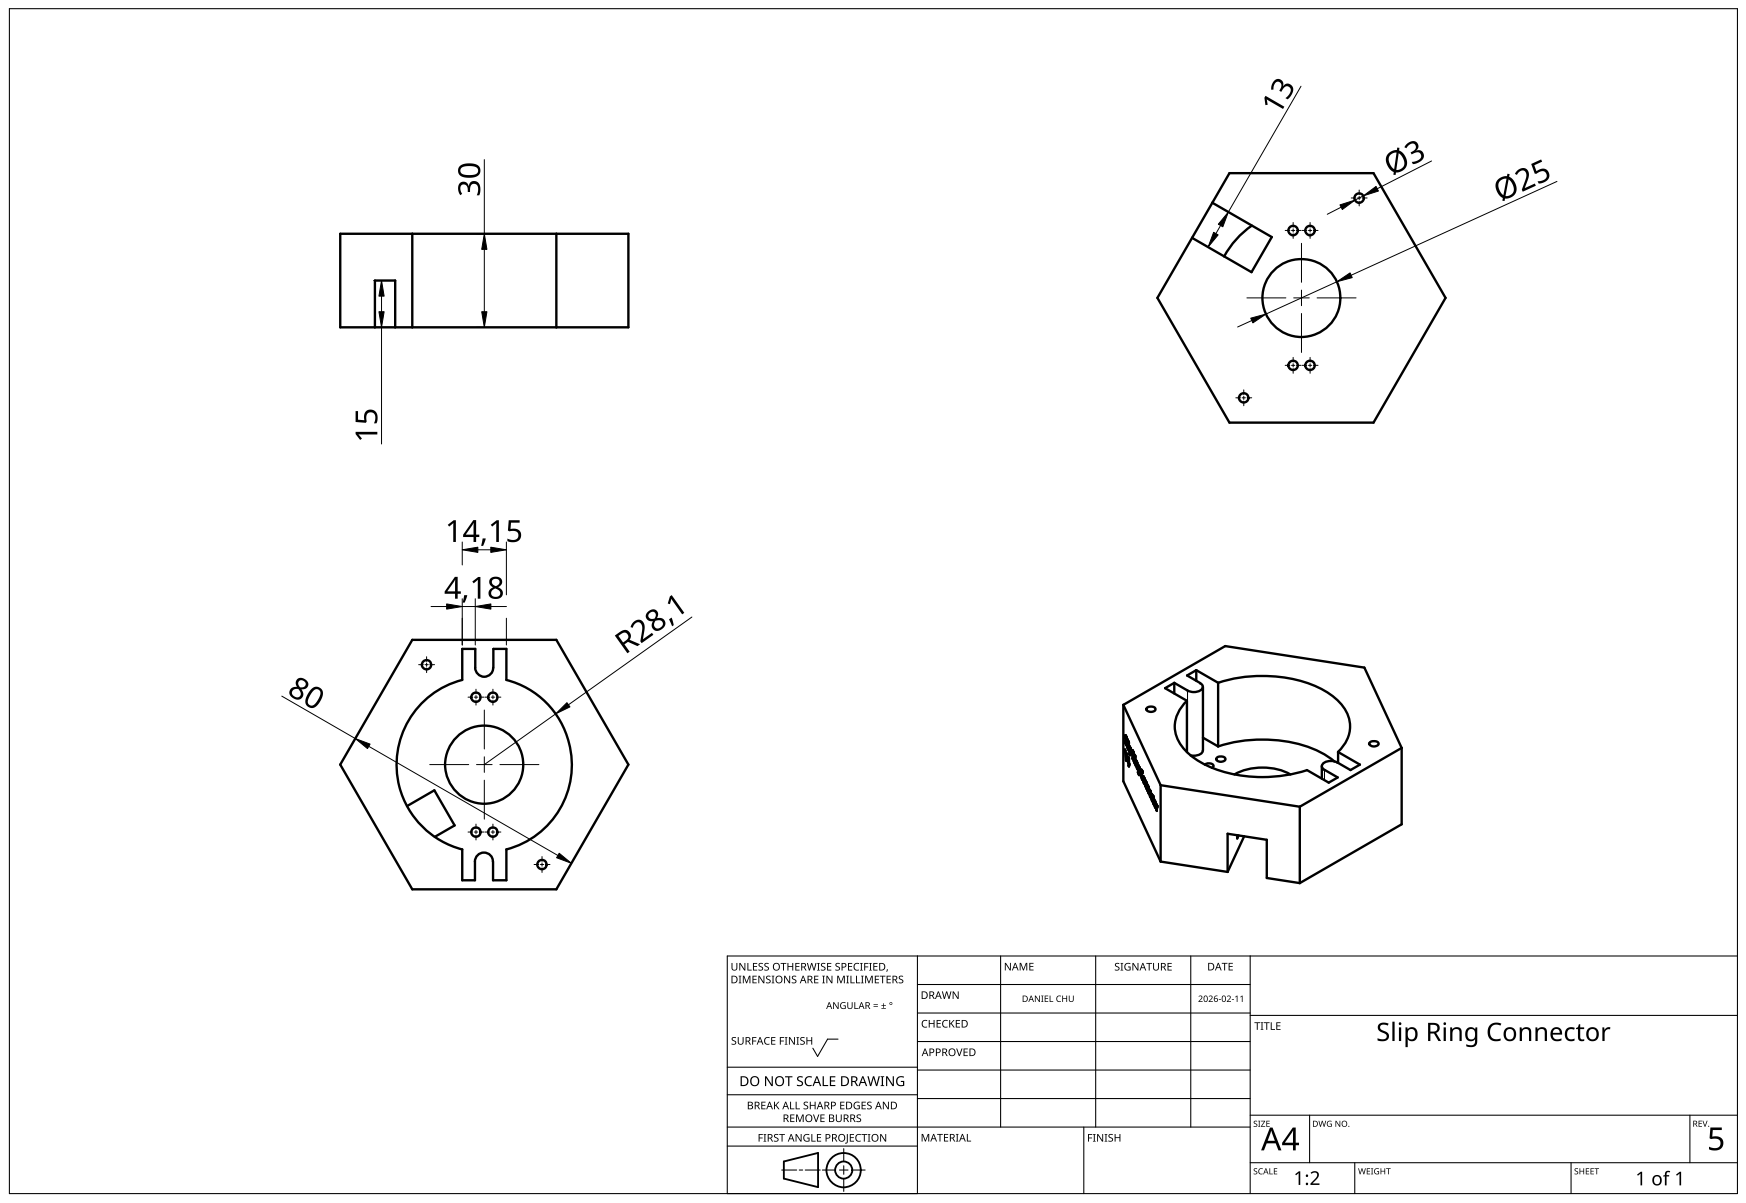
[picture p72: page 1]
