Pegmode/3D-Hologram---NAIT-CMPE2965/Hardware/Mechanical Parts/Motor Mount/Motor connector Drawing V2.pdf

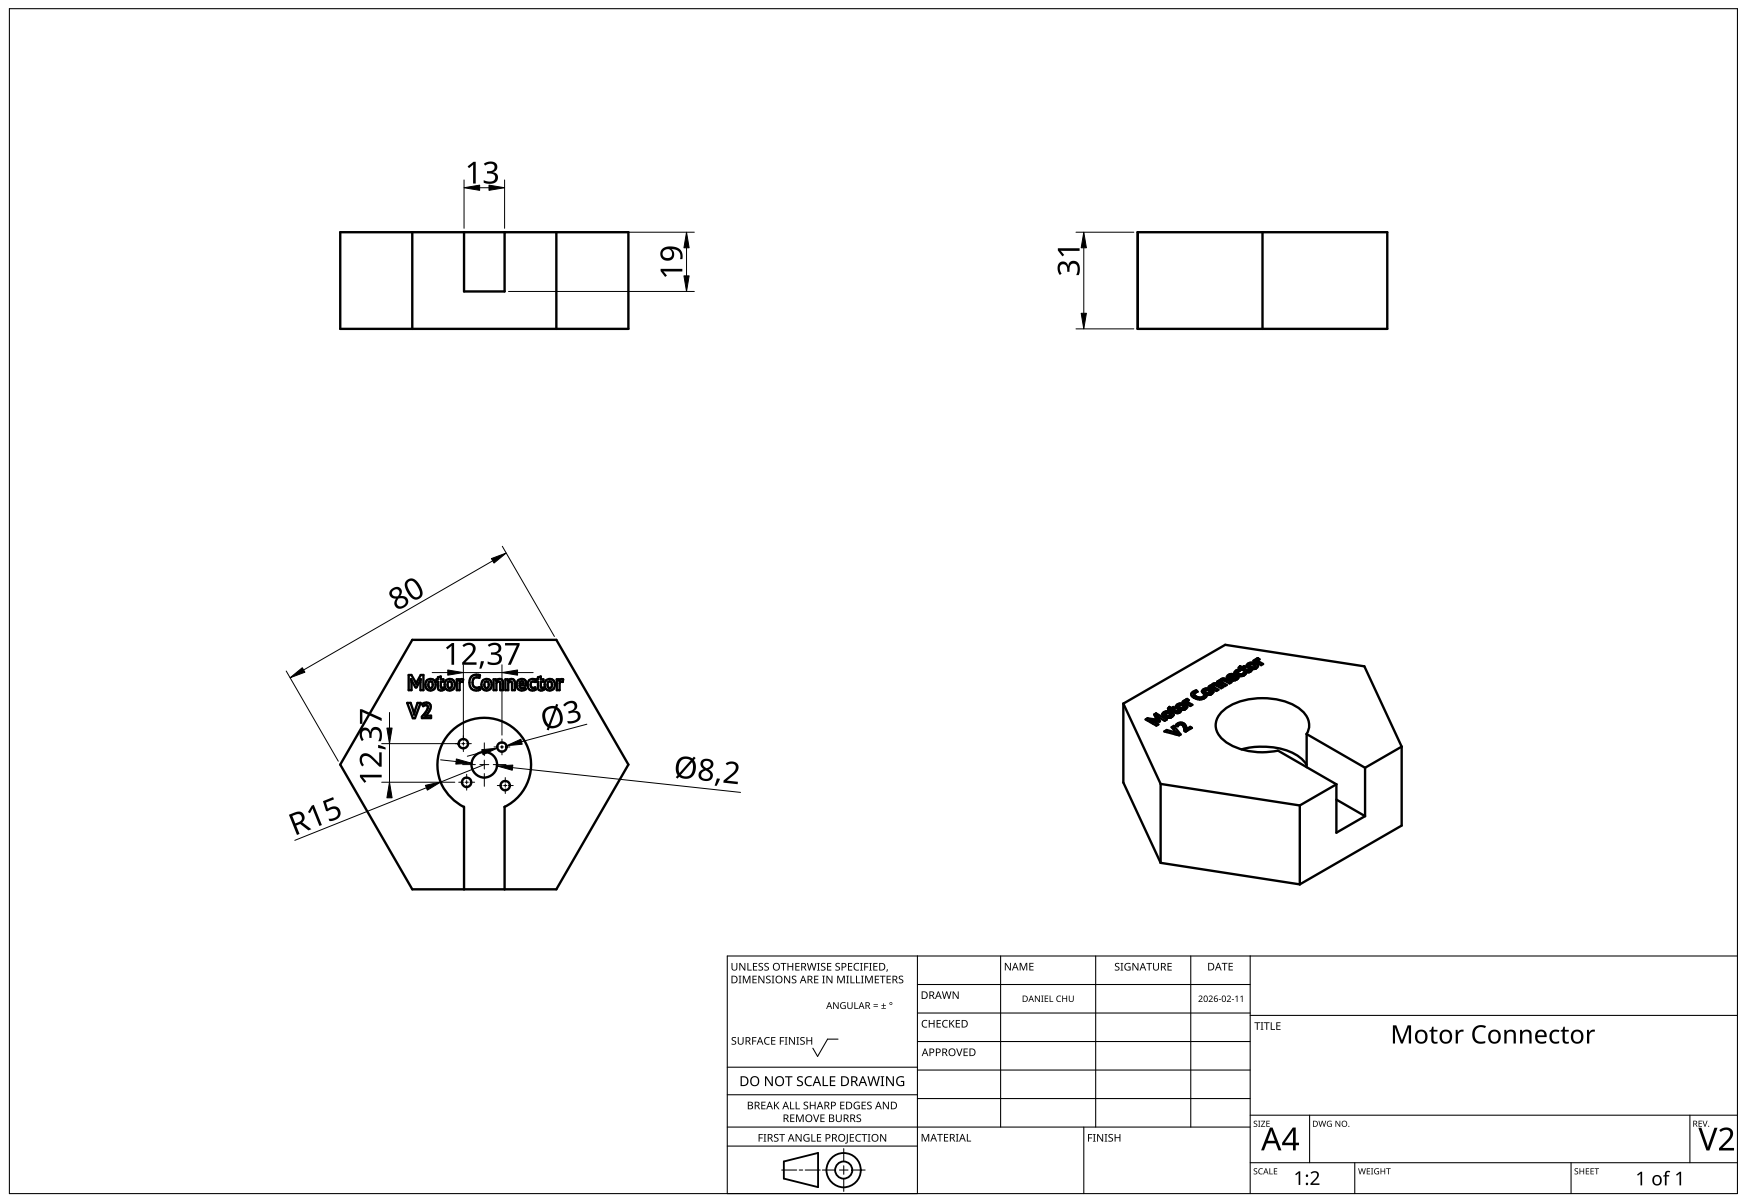
[picture p73: page 1]
