Pegmode/3D-Hologram---NAIT-CMPE2965/Hardware/Mechanical Parts/Slip Ring Connector/Slip Ring Connector Drawing V2.pdf

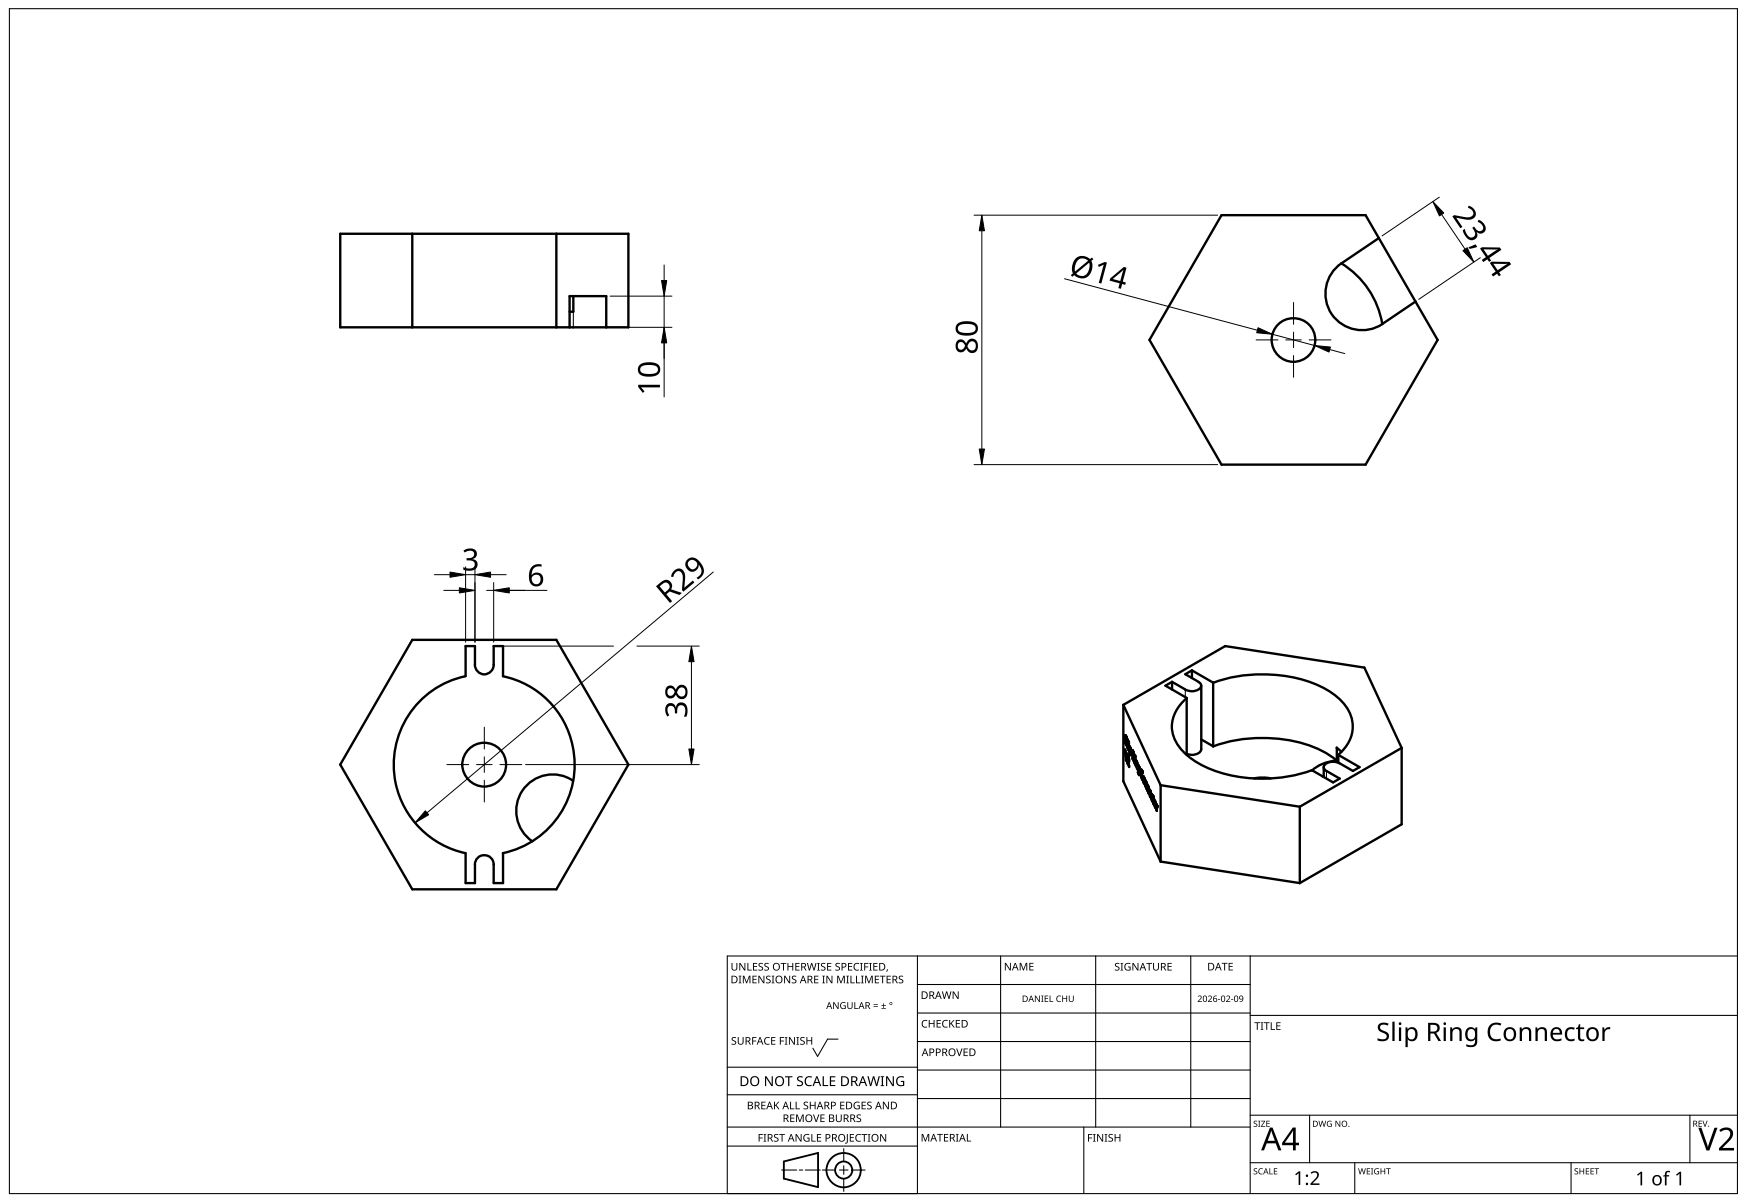
[picture p74: page 1]
