Pegmode/3D-Hologram---NAIT-CMPE2965/Hardware/Mechanical Parts/Slip Ring Connector/Slip Ring Connector Drawing V1.pdf

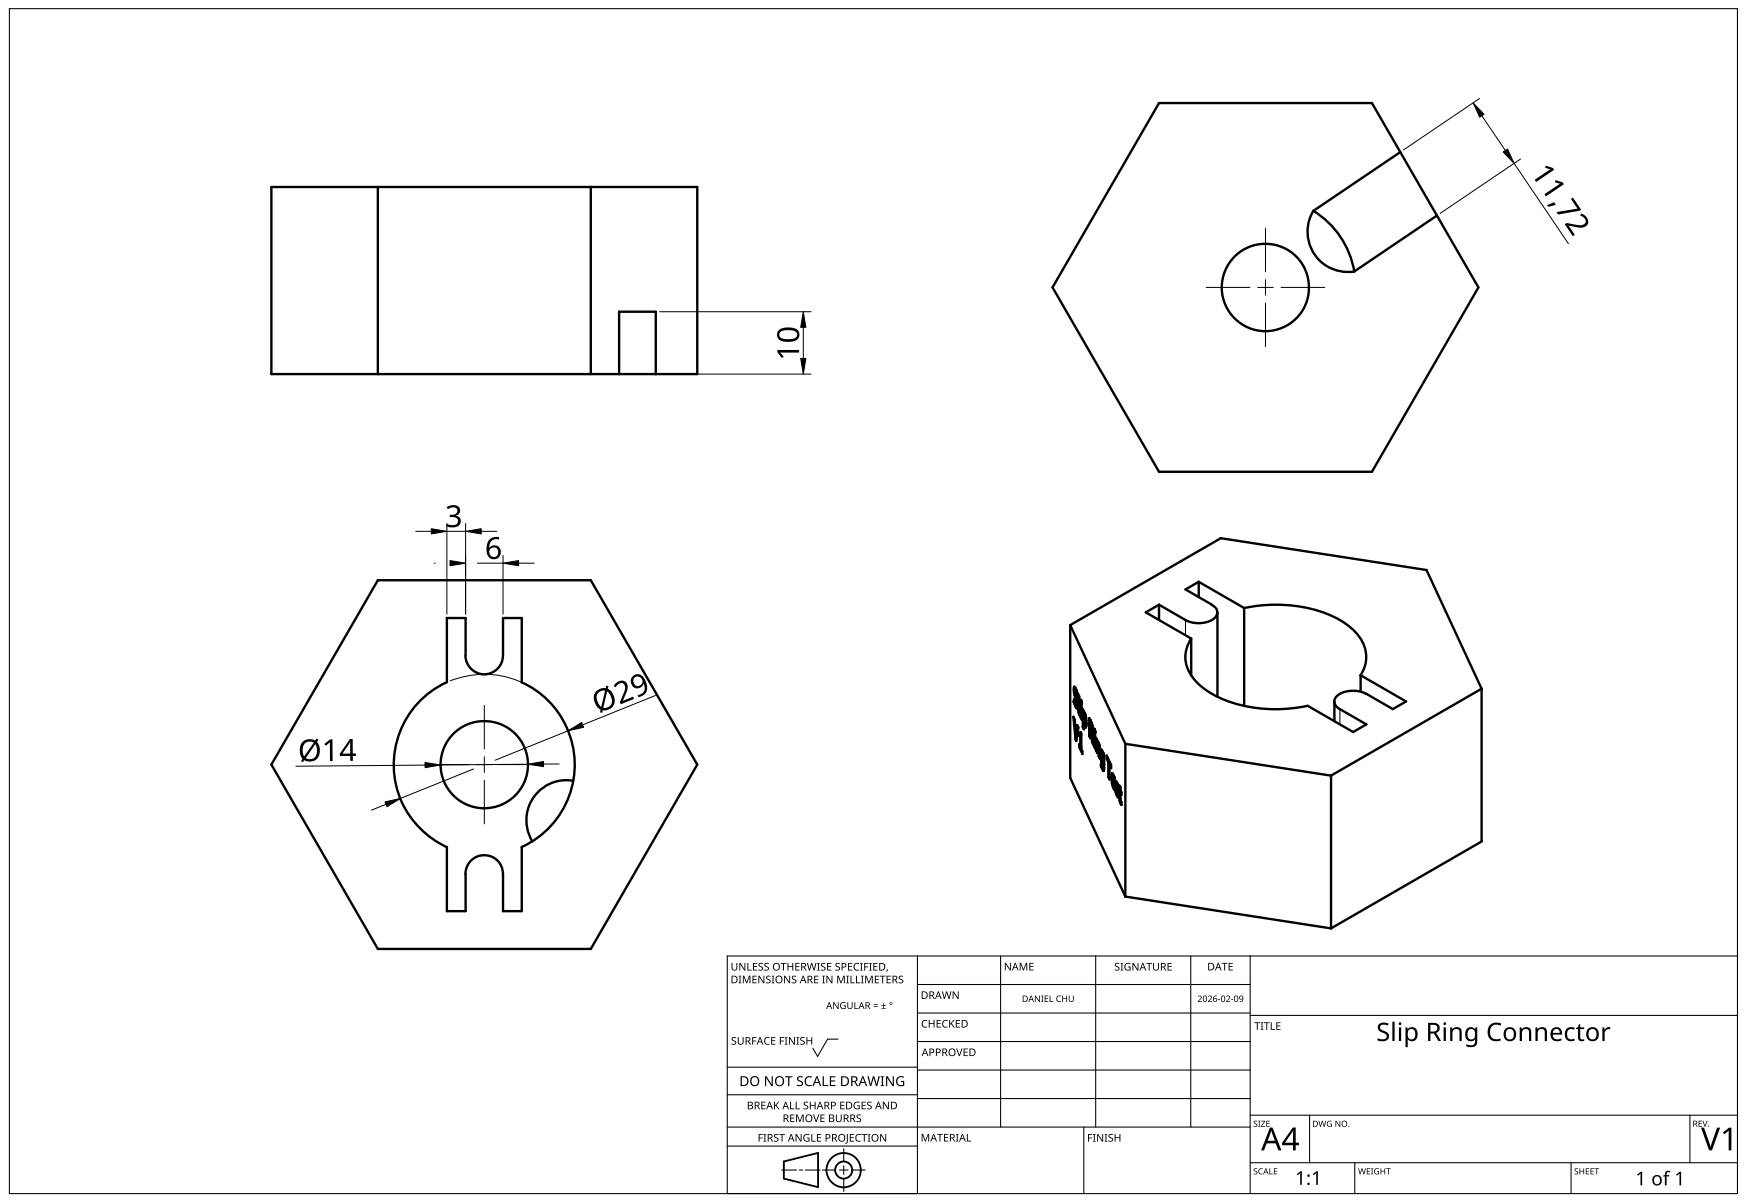
[picture p75: page 1]
