Pegmode/3D-Hologram---NAIT-CMPE2965/Hardware/hologram v3/hologram v3/hologram v3.kicad_sch

## KiCad design Hardware/hologram v3/hologram v3/hologram v3.kicad_sch (2026-03-25)

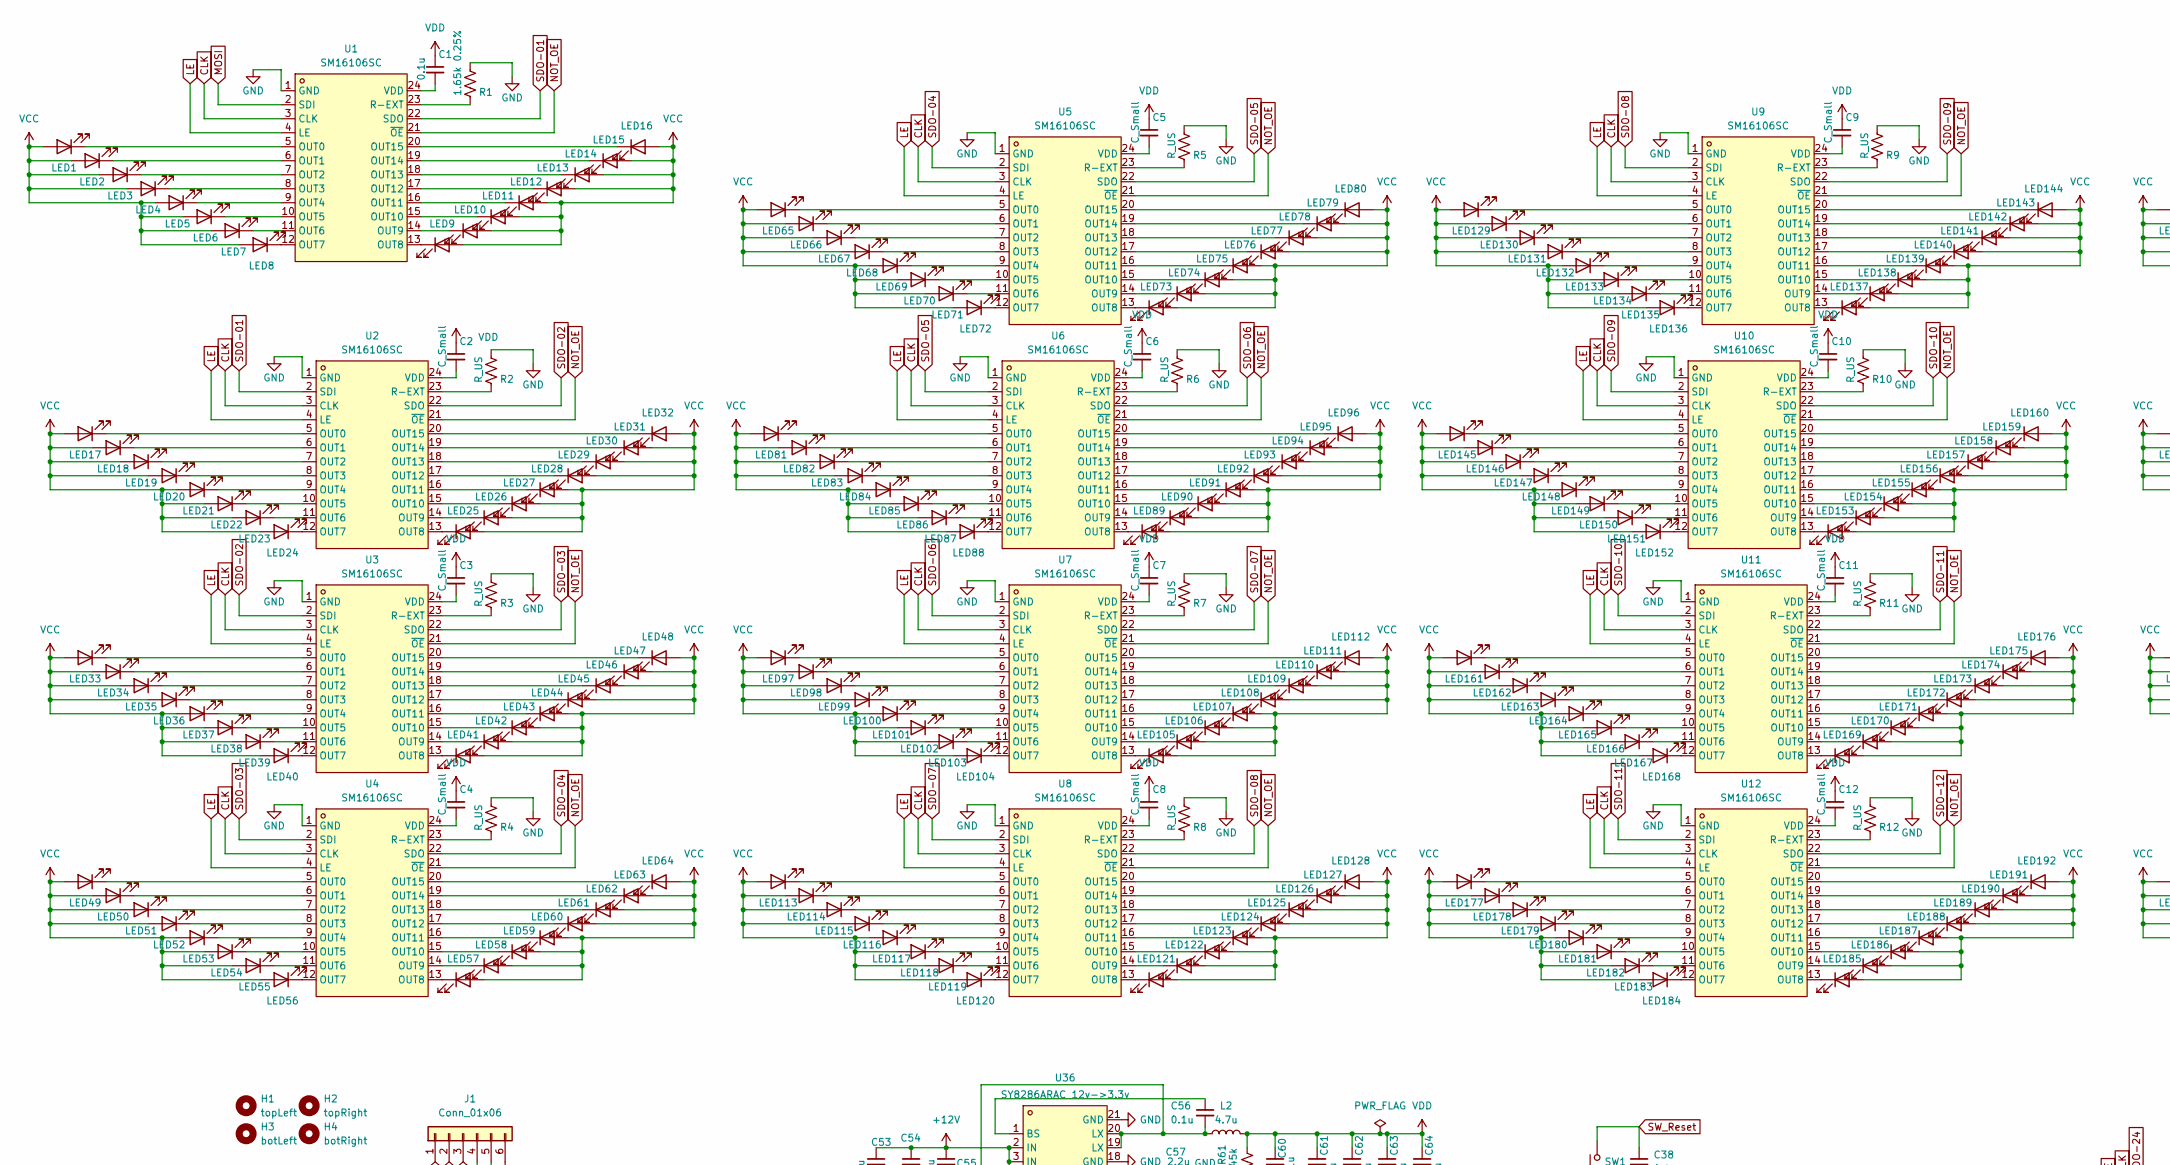
[picture p76: schematic hologram v3.kicad_sch, part in row 1, column 1]

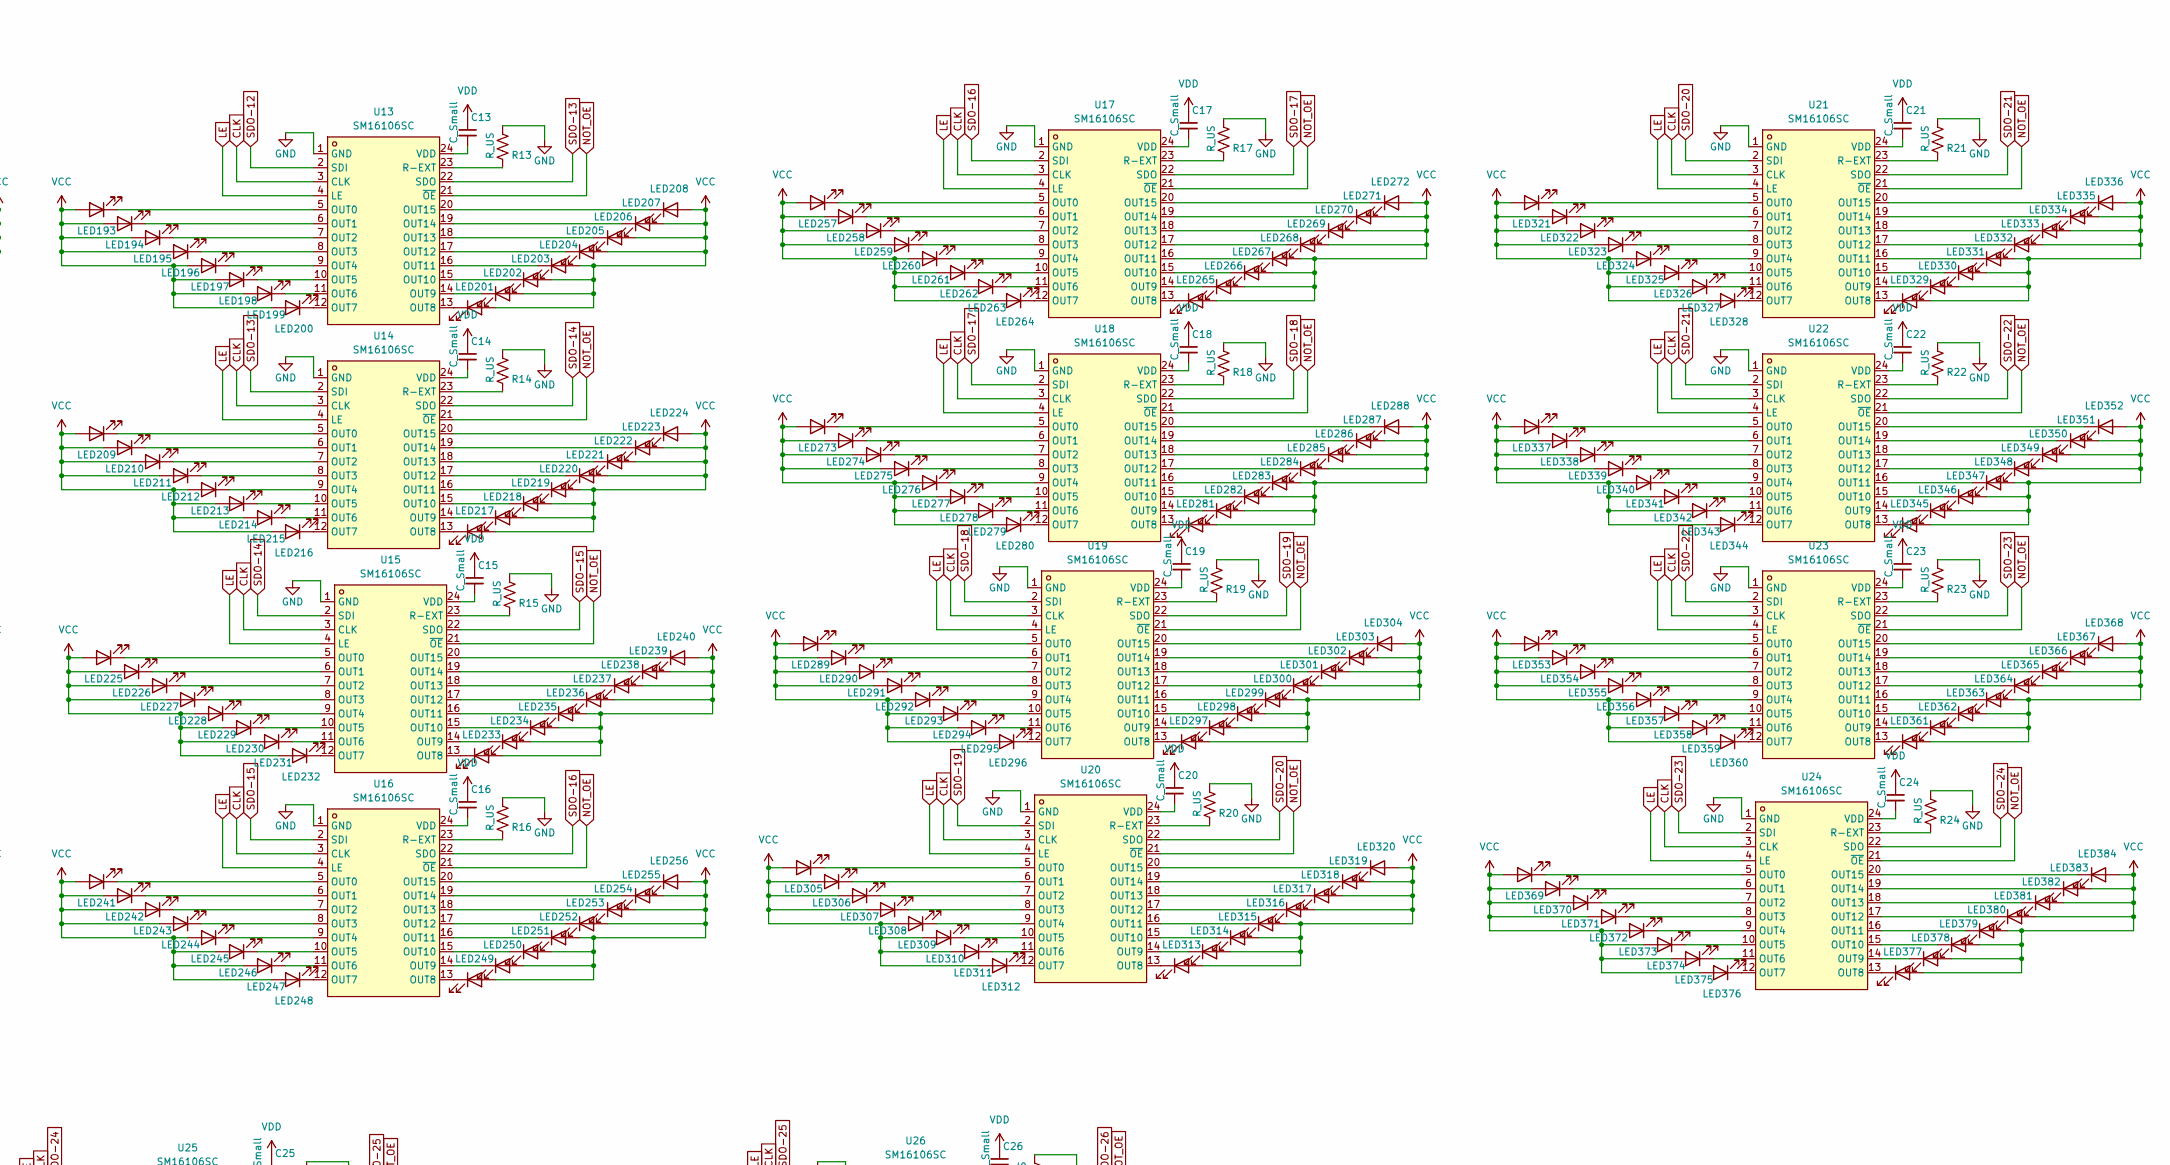
[picture p77: schematic hologram v3.kicad_sch, part in row 1, column 2]

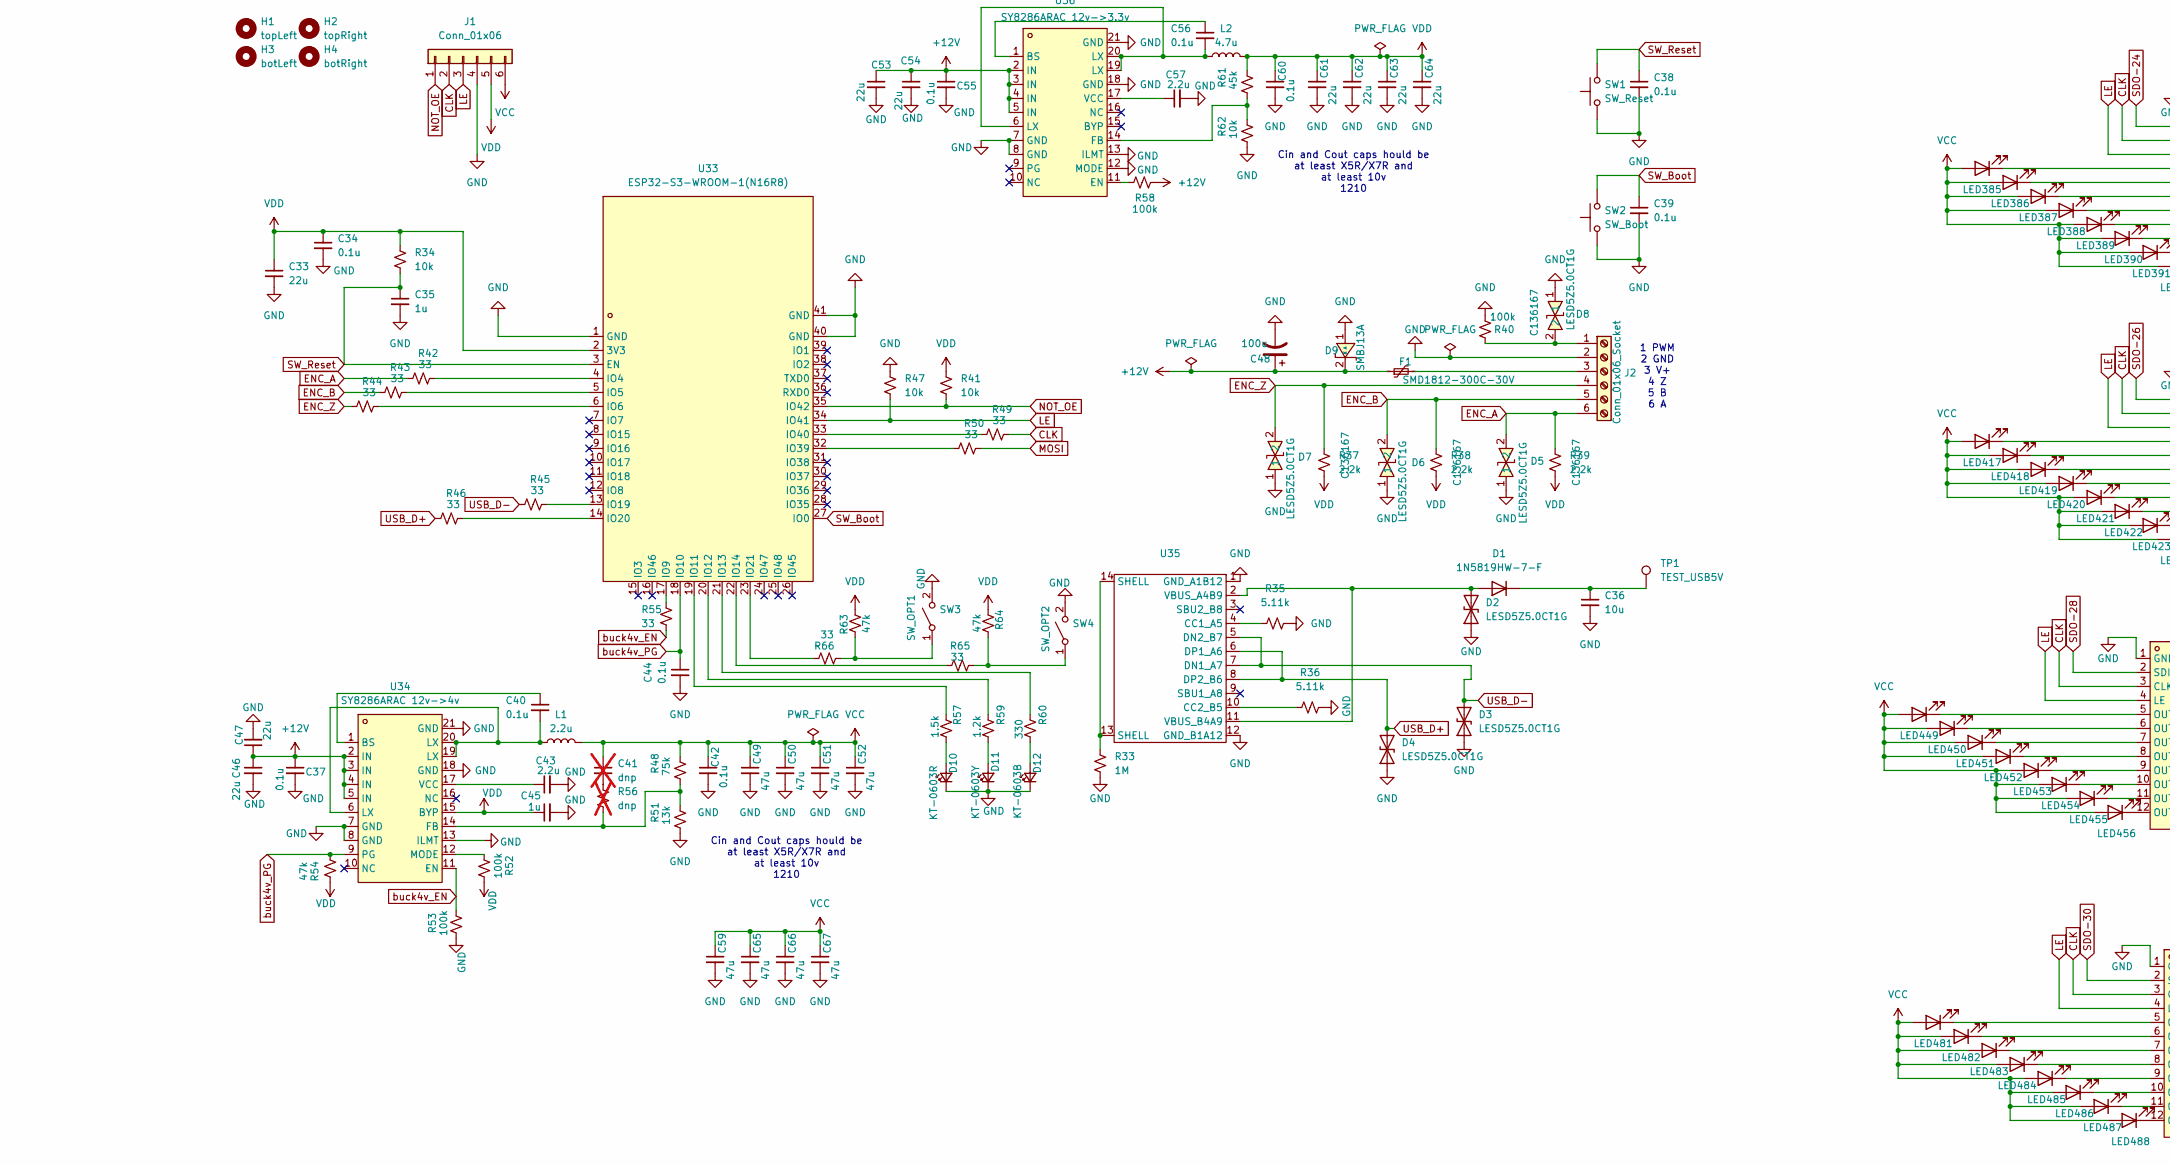
[picture p78: schematic hologram v3.kicad_sch, part in row 2, column 1]

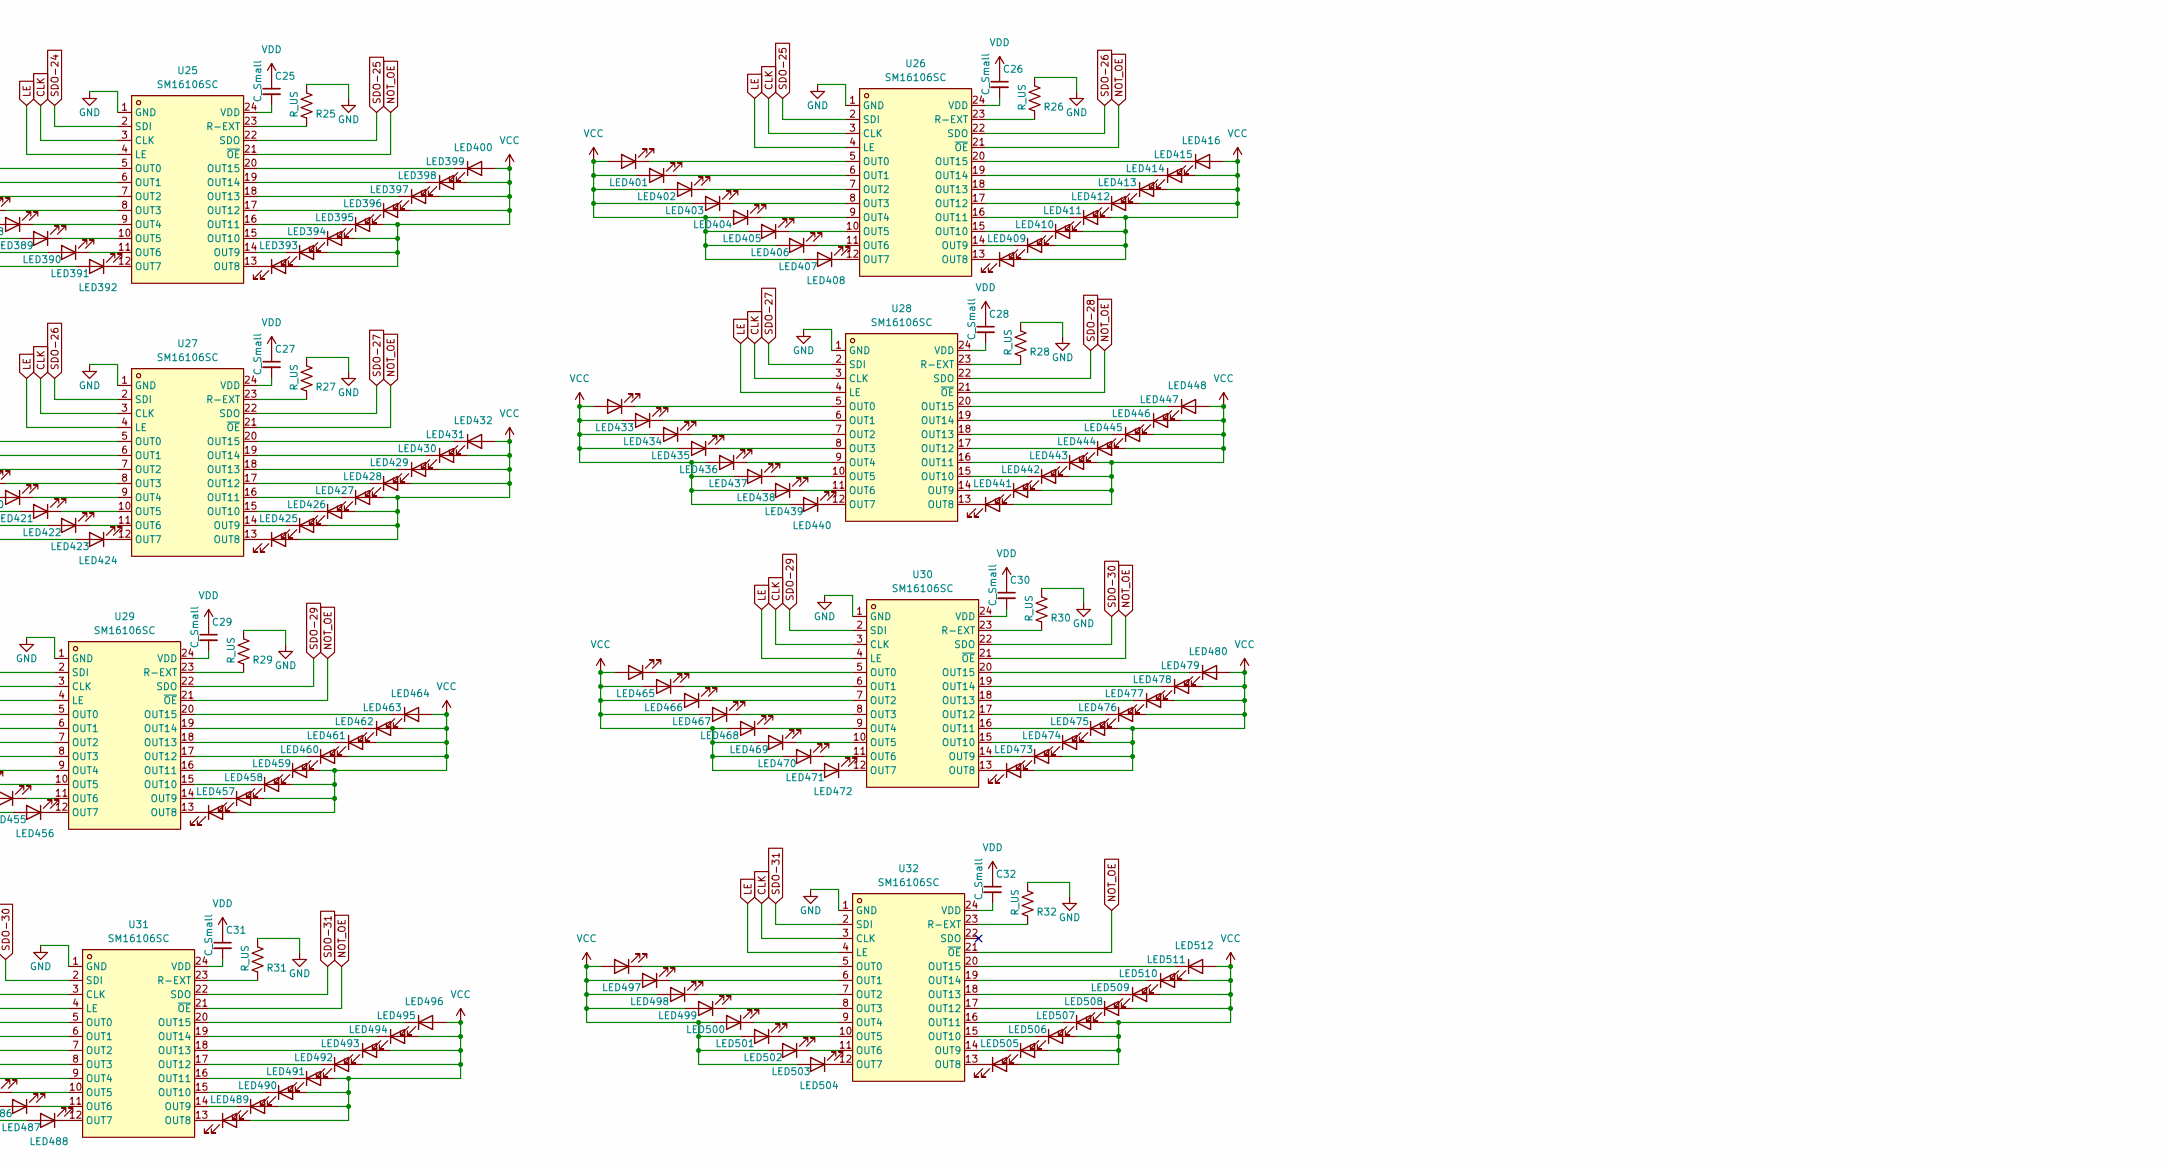
[picture p79: schematic hologram v3.kicad_sch, part in row 2, column 2]

Parts:
C1: 0.1u; C_0603_1608Metric; Part Name CC0603KRX7R9BB104; LCSC Part C14663
C2, C3, C4, C5, C6, C7, C8, C9, C10, C11, C12, C13, C14, C15, C16, C17, C18, C19, C20, C21, C22, C23, C24, C25, C26, C27, C28, C29, C30, C31, C32: C_Small; C_0603_1608Metric; Part Name CC0603KRX7R9BB104; LCSC Part C14663
C33: 22u; C_0805_2012Metric; Part Name CL21A226MAQNNNE; LCSC Part C45783
C34, C37, C38, C39, C40, C42, C44, C55, C56, C60: 0.1u; C_0402_1005Metric; Part Name CL05B104KB54PNC; LCSC Part C307331
C35, C45: 1u; C_0603_1608Metric; Part Name 0603B105K250NT; LCSC Part C59302
C36: 10u; C_0805_2012Metric; Part Name GRM21BR61H106KE43L; LCSC Part C440198
C41: dnp; C_0603_1608Metric; not fitted
C43, C57: 2.2u; C_0603_1608Metric; Part Name GRM188Z71E225KE43D; LCSC Part C415535
C46, C47, C53, C54, C61, C62, C63, C64: 22u; C_1210_3225Metric; Part Name CS3225X7R226K250NRL; LCSC Part C2918511
C48: 100u; CAP-SMD_BD6.3-L6.6-W6.6-LS7.3-FD; Part Name MA25V100M6x6; LCSC Part C46550465
C49, C50, C51, C52, C59, C65, C66, C67: 47u; C_1210_3225Metric; Part Name CS3225X7R476K160NRL; LCSC Part C5440143
D1: 1N5819HW-7-F; SOD-123_L2.7-W1.6-LS3.7-RD; Part Name 1N5819HW-7-F; LCSC Part C82544
D2, D3, D4: LESD5Z5.0CT1G; SOD-523_L1.2-W0.8-LS1.6-BI; Part Name LESD5Z5.0CT1G-HXY; LCSC Part C5451650
D5, D6, D7, D8: LESD5Z5.0CT1G; SOD-523_L1.2-W0.8-LS1.6-BI; Part Name LESD5Z5.0CT1G; LCSC Part C136167
D9: SMBJ13A; SMB_L4.6-W3.6-LS5.3-RD; Part Name SMBJ13A; LCSC Part C151252
D10: KT-0603R; LED_0603_1608Metric; Part Name KT-0603R; LCSC Part C2286
D11: KT-0603Y; LED_0603_1608Metric; Part Name KT-0603Y; LCSC Part C2287
D12: KT-0603B; LED_0603_1608Metric; Part Name KT-0603B; LCSC Part C2288
F1: SMD1812-300C-30V; Fuse_1812_4532Metric; Part Name SMD1812-300C-30V; LCSC Part C47002391
H1: topLeft; MountingHole_5mm_Pad
H2: topRight; MountingHole_5mm_Pad
H3: botLeft; MountingHole_5mm_Pad
H4: botRight; MountingHole_5mm_Pad
J1: Conn_01x06; PinHeader_1x06_P2.54mm_Vertical; Part Name HB-PH3-25416PB2GOP; LCSC Part C6332199
J2: Conn_01x06_Socket; CONN-TH_6P-P5.00_MX128-5.0-06P-GN01-CU-Y-A; Part Name MX128-5.0-06P-GN01-Cu-Y-A; LCSC Part C5290371
L1: 2.2u; IND-SMD_L10.8-W10.0; Part Name CMLO1040H2R2MTT; LCSC Part C439019
L2: 4.7u; IND-SMD_L10.8-W10.0; Part Name CMLO1040H4R7MTT; LCSC Part C439021
LED1, LED2, LED3, LED4, LED5, LED6, LED7, LED8, LED9, LED10, LED11, LED12, LED13, LED14, LED15, LED16, LED17, LED18, LED19, LED20, LED21, LED22, LED23, LED24, LED25, LED26, LED27, LED28, LED29, LED30, LED31, LED32, LED33, LED34, LED35, LED36, LED37, LED38, LED39, LED40, LED41, LED42, LED43, LED44, LED45, LED46, LED47, LED48, LED49, LED50, LED51, LED52, LED53, LED54, LED55, LED56, LED57, LED58, LED59, LED60, LED61, LED62, LED63, LED64, LED65, LED66, LED67, LED68, LED69, LED70, LED71, LED72, LED73, LED74, LED75, LED76, LED77, LED78, LED79, LED80, LED81, LED82, LED83, LED84, LED85, LED86, LED87, LED88, LED89, LED90, LED91, LED92, LED93, LED94, LED95, LED96, LED97, LED98, LED99, LED100, LED101, LED102, LED103, LED104, LED105, LED106, LED107, LED108, LED109, LED110, LED111, LED112, LED113, LED114, LED115, LED116, LED117, LED118, LED119, LED120, LED121, LED122, LED123, LED124, LED125, LED126, LED127, LED128, LED129, LED130, LED131, LED132, LED133, LED134, LED135, LED136, LED137, LED138, LED139, LED140, LED141, LED142, LED143, LED144, LED145, LED146, LED147, LED148, LED149, LED150, LED151, LED152, LED153, LED154, LED155, LED156, LED157, LED158, LED159, LED160, LED161, LED162, LED163, LED164, LED165, LED166, LED167, LED168, LED169, LED170, LED171, LED172, LED173, LED174, LED175, LED176, LED177, LED178, LED179, LED180, LED181, LED182, LED183, LED184, LED185, LED186, LED187, LED188, LED189, LED190, LED191, LED192, LED193, LED194, LED195, LED196, LED197, LED198, LED199, LED200, LED201, LED202, LED203, LED204, LED205, LED206, LED207, LED208, LED209, LED210, LED211, LED212, LED213, LED214, LED215, LED216, LED217, LED218, LED219, LED220, LED221, LED222, LED223, LED224, LED225, LED226, LED227, LED228, LED229, LED230, LED231, LED232, LED233, LED234, LED235, LED236, LED237, LED238, LED239, LED240, LED241, LED242, LED243, LED244, LED245, LED246, LED247, LED248, LED249, LED250, LED251, LED252, LED253, LED254, LED255, LED256, LED257, LED258, LED259, LED260, LED261, LED262, LED263, LED264, LED265, LED266, LED267, LED268, LED269, LED270, LED271, LED272, LED273, LED274, LED275, LED276, LED277, LED278, LED279, LED280, LED281, LED282, LED283, LED284, LED285, LED286, LED287, LED288, LED289, LED290, LED291, LED292, LED293, LED294, LED295, LED296, LED297, LED298, LED299, LED300, LED301, LED302, LED303, LED304, LED305, LED306, LED307, LED308, LED309, LED310, LED311, LED312, LED313, LED314, LED315, LED316, LED317, LED318, LED319, LED320, LED321, LED322, LED323, LED324, LED325, LED326, LED327, LED328, LED329, LED330, LED331, LED332, LED333, LED334, LED335, LED336, LED337, LED338, LED339, LED340, LED341, LED342, LED343, LED344, LED345, LED346, LED347, LED348, LED349, LED350, LED351, LED352, LED353, LED354, LED355, LED356, LED357, LED358, LED359, LED360, LED361, LED362, LED363, LED364, LED365, LED366, LED367, LED368, LED369, LED370, LED371, LED372, LED373, LED374, LED375, LED376, LED377, LED378, LED379, LED380, LED381, LED382, LED383, LED384, LED385, LED386, LED387, LED388, LED389, LED390, LED391, LED392, LED393, LED394, LED395, LED396, LED397, LED398, LED399, LED400, LED401, LED402, LED403, LED404, LED405, LED406, LED407, LED408, LED409, LED410, LED411, LED412, LED413, LED414, LED415, LED416, LED417, LED418, LED419, LED420, LED421, LED422, LED423, LED424, LED425, LED426, LED427, LED428, LED429, LED430, LED431, LED432, LED433, LED434, LED435, LED436, LED437, LED438, LED439, LED440, LED441, LED442, LED443, LED444, LED445, LED446, LED447, LED448, LED449, LED450, LED451, LED452, LED453, LED454, LED455, LED456, LED457, LED458, LED459, LED460, LED461, LED462, LED463, LED464, LED465, LED466, LED467, LED468, LED469, LED470, LED471, LED472, LED473, LED474, LED475, LED476, LED477, LED478, LED479, LED480, LED481, LED482, LED483, LED484, LED485, LED486, LED487, LED488, LED489, LED490, LED491, LED492, LED493, LED494, LED495, LED496, LED497, LED498, LED499, LED500, LED501, LED502, LED503, LED504, LED505, LED506, LED507, LED508, LED509, LED510, LED511, LED512: 0805G (Green); LED0805-RD-flipped; Part Name A-SC170ZB1D-A02-3T; LCSC Part C5355441
R1: 1.65k 0.25%; R_0603_1608Metric; Part Name RT0603BRD071K65L; LCSC Part C705743
R2, R3, R4, R5, R6, R7, R8, R9, R10, R11, R12, R13, R14, R15, R16, R17, R18, R19, R20, R21, R22, R23, R24, R25, R26, R27, R28, R29, R30, R31, R32: R_US; R_0603_1608Metric; Part Name RT0603BRD071K65L; LCSC Part C705743
R33: 1M; R_0603_1608Metric; Part Name 0603WAF1004T5E; LCSC Part C22935
R34, R41, R47, R62: 10k; R_0603_1608Metric; Part Name FRH0603B1002TS; LCSC Part C5126214
R35, R36: 5.11k; R_0603_1608Metric; Part Name 0603WAF5101T5E; LCSC Part C23186
R37, R38, R39: 2.2k; R_0603_1608Metric; Part Name 0603WAF2201T5E; LCSC Part C4190
R40, R52, R53, R58: 100k; R_0603_1608Metric; Part Name 0603WAF1003T5E; LCSC Part C25803
R42, R43, R44, R45, R46, R49, R50, R55, R65, R66: 33; R_0402_1005Metric; Part Name 0402WGF330JTCE; LCSC Part C25105
R48: 75k; R_0603_1608Metric; Part Name RT0603BRD0775KL; LCSC Part C723587
R51: 13k; R_0603_1608Metric; Part Name TC0325B1302T5F; LCSC Part C50670543
R54, R63, R64: 47k; R_0603_1608Metric; Part Name 0603WAF4702T5E; LCSC Part C25819
R56: dnp; R_0603_1608Metric; not fitted
R57: 1.5k; R_0603_1608Metric; Part Name 0603WAF1501T5E; LCSC Part C22843
R59: 1.2k; R_0603_1608Metric; Part Name 0603WAF1201T5E; LCSC Part C22765
R60: 330; R_0603_1608Metric; Part Name 0603WAF3300T5E; LCSC Part C23138
R61: 45k; R_0603_1608Metric; Part Name RT0603BRD0745K3L; LCSC Part C861415
SW1: SW_Reset; KEY-SMD_L4.0-W3.0-LS4.9-1; Part Name HX 3x4x2-2P-1.6N TACTILE SWITCH; LCSC Part C49234124
SW2: SW_Boot; KEY-SMD_L4.0-W3.0-LS4.9-1; Part Name HX 3x4x2-2P-1.6N TACTILE SWITCH; LCSC Part C49234124
SW3: SW_OPT1; KEY-SMD_L4.0-W3.0-LS4.9-1; Part Name HX 3x4x2-2P-1.6N TACTILE SWITCH; LCSC Part C49234124
SW4: SW_OPT2; KEY-SMD_L4.0-W3.0-LS4.9-1; Part Name HX 3x4x2-2P-1.6N TACTILE SWITCH; LCSC Part C49234124
TP1: TEST_USB5V; TestPoint_Pad_3.0x3.0mm
U1, U2, U3, U4, U5, U6, U7, U8, U9, U10, U11, U12, U13, U14, U15, U16, U17, U18, U19, U20, U21, U22, U23, U24, U25, U26, U27, U28, U29, U30, U31, U32: SM16106SC; QSOP-24_L8.7-W4.0-P0.64-LS6.0-BL; Part Name SM16206S; LCSC Part C121618
U33: ESP32-S3-WROOM-1(N16R8); WIRELM-SMD_ESP32-S3-WROOM-1; Part Name ESP32-S3-WROOM-1-N16R8; LCSC Part C2913202
U34: SY8286ARAC 12v->4v; QFN-20_L3.0-W3.0-P0.45-BL-EP1.0; Part Name SY8286ARAC; LCSC Part C178251
U35: USB-C-SMD_TYPE-C-6PIN-2MD-073; Part Name TYPE-C 16PIN 2MD(073); LCSC Part C2765186
U36: SY8286ARAC 12v->3.3v; QFN-20_L3.0-W3.0-P0.45-BL-EP1.0; Part Name SY8286ARAC; LCSC Part C178251

Connections:
+12V: C37.1, C46.1, C47.1, C48.1, C53.1, C54.1, C55.1, D9.2 (K), F1.1, R58.1, U34.2 (IN), U34.3 (IN), U34.4 (IN), U34.5 (IN), U36.2 (IN), U36.3 (IN), U36.4 (IN), U36.5 (IN)
CLK: J1.2, R49.1, U1.3 (CLK), U2.3 (CLK), U3.3 (CLK), U4.3 (CLK), U5.3 (CLK), U6.3 (CLK), U7.3 (CLK), U8.3 (CLK), U9.3 (CLK), U10.3 (CLK), U11.3 (CLK), U12.3 (CLK), U13.3 (CLK), U14.3 (CLK), U15.3 (CLK), U16.3 (CLK), U17.3 (CLK), U18.3 (CLK), U19.3 (CLK), U20.3 (CLK), U21.3 (CLK), U22.3 (CLK), U23.3 (CLK), U24.3 (CLK), U25.3 (CLK), U26.3 (CLK), U27.3 (CLK), U28.3 (CLK), U29.3 (CLK), U30.3 (CLK), U31.3 (CLK), U32.3 (CLK)
ENC_A: D5.2, J2.6, R39.1, R42.2
ENC_B: D6.2, J2.5, R38.1, R43.2
ENC_Z: D7.2, J2.4, R37.1, R44.2
GND: C33.2, C34.2, C35.2, C36.2, C37.2, C38.2, C39.2, C42.2, C43.2, C44.2, C45.2, C46.2, C47.2, C48.2, C49.2, C50.2, C51.2, C52.2, C53.2, C54.2, C55.2, C57.2, C59.2, C60.2, C61.2, C62.2, C63.2, C64.2, C65.2, C66.2, C67.2, D2.1 (A1), D3.1 (A1), D4.1 (A1), D5.1, D6.1, D7.1, D8.1, D9.1 (A), D10.1 (K), D11.1 (K), D12.1 (K), J1.4, J2.2, R1.1, R2.1, R3.1, R4.1, R5.1, R6.1, R7.1, R8.1, R9.1, R10.1, R11.1, R12.1, R13.1, R14.1, R15.1, R16.1, R17.1, R18.1, R19.1, R20.1, R21.1, R22.1, R23.1, R24.1, R25.1, R26.1, R27.1, R28.1, R29.1, R30.1, R31.1, R32.1, R33.2, R35.2, R36.2, R40.1, R47.1, R51.2, R53.2, R62.2, SW1.1, SW2.1, SW3.2 (B), SW4.2 (B), U1.1 (GND), U2.1 (GND), U3.1 (GND), U4.1 (GND), U5.1 (GND), U6.1 (GND), U7.1 (GND), U8.1 (GND), U9.1 (GND), U10.1 (GND), U11.1 (GND), U12.1 (GND), U13.1 (GND), U14.1 (GND), U15.1 (GND), U16.1 (GND), U17.1 (GND), U18.1 (GND), U19.1 (GND), U20.1 (GND), U21.1 (GND), U22.1 (GND), U23.1 (GND), U24.1 (GND), U25.1 (GND), U26.1 (GND), U27.1 (GND), U28.1 (GND), U29.1 (GND), U30.1 (GND), U31.1 (GND), U32.1 (GND), U33.1 (GND), U33.40 (GND), U33.41 (GND), U34.7 (GND), U34.8 (GND), U34.13 (ILMT), U34.18 (GND), U34.21 (GND), U35.1 (GND_A1B12), U35.12 (GND_B1A12), U36.7 (GND), U36.8 (GND), U36.12 (MODE), U36.13 (ILMT), U36.18 (GND), U36.21 (GND)
LE: J1.3, R47.2, U1.4 (LE), U2.4 (LE), U3.4 (LE), U4.4 (LE), U5.4 (LE), U6.4 (LE), U7.4 (LE), U8.4 (LE), U9.4 (LE), U10.4 (LE), U11.4 (LE), U12.4 (LE), U13.4 (LE), U14.4 (LE), U15.4 (LE), U16.4 (LE), U17.4 (LE), U18.4 (LE), U19.4 (LE), U20.4 (LE), U21.4 (LE), U22.4 (LE), U23.4 (LE), U24.4 (LE), U25.4 (LE), U26.4 (LE), U27.4 (LE), U28.4 (LE), U29.4 (LE), U30.4 (LE), U31.4 (LE), U32.4 (LE), U33.34 (IO41)
MOSI: R50.1, U1.2 (SDI)
NOT_OE: J1.1, R41.2, U1.21 (~OE), U2.21 (~OE), U3.21 (~OE), U4.21 (~OE), U5.21 (~OE), U6.21 (~OE), U7.21 (~OE), U8.21 (~OE), U9.21 (~OE), U10.21 (~OE), U11.21 (~OE), U12.21 (~OE), U13.21 (~OE), U14.21 (~OE), U15.21 (~OE), U16.21 (~OE), U17.21 (~OE), U18.21 (~OE), U19.21 (~OE), U20.21 (~OE), U21.21 (~OE), U22.21 (~OE), U23.21 (~OE), U24.21 (~OE), U25.21 (~OE), U26.21 (~OE), U27.21 (~OE), U28.21 (~OE), U29.21 (~OE), U30.21 (~OE), U31.21 (~OE), U32.21 (~OE), U33.35 (IO42)
unnamed: C1.2, U1.24 (VDD)
unnamed: C2.2, U2.24 (VDD)
unnamed: C3.2, U3.24 (VDD)
unnamed: C4.2, U4.24 (VDD)
unnamed: C5.2, U5.24 (VDD)
unnamed: C6.2, U6.24 (VDD)
unnamed: C7.2, U7.24 (VDD)
unnamed: C8.2, U8.24 (VDD)
unnamed: C9.2, U9.24 (VDD)
unnamed: C10.2, U10.24 (VDD)
unnamed: C11.2, U11.24 (VDD)
unnamed: C12.2, U12.24 (VDD)
unnamed: C13.2, U13.24 (VDD)
unnamed: C14.2, U14.24 (VDD)
unnamed: C15.2, U15.24 (VDD)
unnamed: C16.2, U16.24 (VDD)
unnamed: C17.2, U17.24 (VDD)
unnamed: C18.2, U18.24 (VDD)
unnamed: C19.2, U19.24 (VDD)
unnamed: C20.2, U20.24 (VDD)
unnamed: C21.2, U21.24 (VDD)
unnamed: C22.2, U22.24 (VDD)
unnamed: C23.2, U23.24 (VDD)
unnamed: C24.2, U24.24 (VDD)
unnamed: C25.2, U25.24 (VDD)
unnamed: C26.2, U26.24 (VDD)
unnamed: C27.2, U27.24 (VDD)
unnamed: C28.2, U28.24 (VDD)
unnamed: C29.2, U29.24 (VDD)
unnamed: C30.2, U30.24 (VDD)
unnamed: C31.2, U31.24 (VDD)
unnamed: C32.2, U32.24 (VDD)
unnamed: C36.1, D1.1 (K), TP1.1
unnamed: C40.1, U34.1 (BS)
unnamed: C40.2, L1.1, U34.6 (LX), U34.19 (LX), U34.20 (LX)
unnamed: C41.2, R56.1
unnamed: C43.1, U34.17 (VCC)
unnamed: C56.1, U36.1 (BS)
unnamed: C56.2, L2.1, U36.6 (LX), U36.19 (LX), U36.20 (LX)
unnamed: C57.1, U36.17 (VCC)
unnamed: D1.2 (A), D2.2 (A2), U35.2 (VBUS_A4B9), U35.11 (VBUS_B4A9)
unnamed: D8.2, J2.1, R40.2
unnamed: D10.2 (A), R57.2
unnamed: D11.2 (A), R59.2
unnamed: D12.2 (A), R60.2
unnamed: F1.2, J2.3
unnamed: LED1.1 (K), U1.5 (OUT0)
unnamed: LED2.1 (K), U1.6 (OUT1)
unnamed: LED3.1 (K), U1.7 (OUT2)
unnamed: LED4.1 (K), U1.8 (OUT3)
unnamed: LED5.1 (K), U1.9 (OUT4)
unnamed: LED6.1 (K), U1.10 (OUT5)
unnamed: LED7.1 (K), U1.11 (OUT6)
unnamed: LED8.1 (K), U1.12 (OUT7)
unnamed: LED9.1 (K), U1.13 (OUT8)
unnamed: LED10.1 (K), U1.14 (OUT9)
unnamed: LED11.1 (K), U1.15 (OUT10)
unnamed: LED12.1 (K), U1.16 (OUT11)
unnamed: LED13.1 (K), U1.17 (OUT12)
unnamed: LED14.1 (K), U1.18 (OUT13)
unnamed: LED15.1 (K), U1.19 (OUT14)
unnamed: LED16.1 (K), U1.20 (OUT15)
unnamed: LED17.1 (K), U2.5 (OUT0)
unnamed: LED18.1 (K), U2.6 (OUT1)
unnamed: LED19.1 (K), U2.7 (OUT2)
unnamed: LED20.1 (K), U2.8 (OUT3)
unnamed: LED21.1 (K), U2.9 (OUT4)
unnamed: LED22.1 (K), U2.10 (OUT5)
unnamed: LED23.1 (K), U2.11 (OUT6)
unnamed: LED24.1 (K), U2.12 (OUT7)
unnamed: LED25.1 (K), U2.13 (OUT8)
unnamed: LED26.1 (K), U2.14 (OUT9)
unnamed: LED27.1 (K), U2.15 (OUT10)
unnamed: LED28.1 (K), U2.16 (OUT11)
unnamed: LED29.1 (K), U2.17 (OUT12)
unnamed: LED30.1 (K), U2.18 (OUT13)
unnamed: LED31.1 (K), U2.19 (OUT14)
unnamed: LED32.1 (K), U2.20 (OUT15)
unnamed: LED33.1 (K), U3.5 (OUT0)
unnamed: LED34.1 (K), U3.6 (OUT1)
unnamed: LED35.1 (K), U3.7 (OUT2)
unnamed: LED36.1 (K), U3.8 (OUT3)
unnamed: LED37.1 (K), U3.9 (OUT4)
unnamed: LED38.1 (K), U3.10 (OUT5)
unnamed: LED39.1 (K), U3.11 (OUT6)
unnamed: LED40.1 (K), U3.12 (OUT7)
unnamed: LED41.1 (K), U3.13 (OUT8)
unnamed: LED42.1 (K), U3.14 (OUT9)
unnamed: LED43.1 (K), U3.15 (OUT10)
unnamed: LED44.1 (K), U3.16 (OUT11)
unnamed: LED45.1 (K), U3.17 (OUT12)
unnamed: LED46.1 (K), U3.18 (OUT13)
unnamed: LED47.1 (K), U3.19 (OUT14)
unnamed: LED48.1 (K), U3.20 (OUT15)
unnamed: LED49.1 (K), U4.5 (OUT0)
unnamed: LED50.1 (K), U4.6 (OUT1)
unnamed: LED51.1 (K), U4.7 (OUT2)
unnamed: LED52.1 (K), U4.8 (OUT3)
unnamed: LED53.1 (K), U4.9 (OUT4)
unnamed: LED54.1 (K), U4.10 (OUT5)
unnamed: LED55.1 (K), U4.11 (OUT6)
unnamed: LED56.1 (K), U4.12 (OUT7)
unnamed: LED57.1 (K), U4.13 (OUT8)
unnamed: LED58.1 (K), U4.14 (OUT9)
unnamed: LED59.1 (K), U4.15 (OUT10)
unnamed: LED60.1 (K), U4.16 (OUT11)
unnamed: LED61.1 (K), U4.17 (OUT12)
unnamed: LED62.1 (K), U4.18 (OUT13)
unnamed: LED63.1 (K), U4.19 (OUT14)
unnamed: LED64.1 (K), U4.20 (OUT15)
unnamed: LED65.1 (K), U5.5 (OUT0)
unnamed: LED66.1 (K), U5.6 (OUT1)
unnamed: LED67.1 (K), U5.7 (OUT2)
unnamed: LED68.1 (K), U5.8 (OUT3)
unnamed: LED69.1 (K), U5.9 (OUT4)
unnamed: LED70.1 (K), U5.10 (OUT5)
unnamed: LED71.1 (K), U5.11 (OUT6)
unnamed: LED72.1 (K), U5.12 (OUT7)
unnamed: LED73.1 (K), U5.13 (OUT8)
unnamed: LED74.1 (K), U5.14 (OUT9)
unnamed: LED75.1 (K), U5.15 (OUT10)
unnamed: LED76.1 (K), U5.16 (OUT11)
unnamed: LED77.1 (K), U5.17 (OUT12)
unnamed: LED78.1 (K), U5.18 (OUT13)
unnamed: LED79.1 (K), U5.19 (OUT14)
unnamed: LED80.1 (K), U5.20 (OUT15)
unnamed: LED81.1 (K), U6.5 (OUT0)
unnamed: LED82.1 (K), U6.6 (OUT1)
unnamed: LED83.1 (K), U6.7 (OUT2)
unnamed: LED84.1 (K), U6.8 (OUT3)
unnamed: LED85.1 (K), U6.9 (OUT4)
unnamed: LED86.1 (K), U6.10 (OUT5)
unnamed: LED87.1 (K), U6.11 (OUT6)
unnamed: LED88.1 (K), U6.12 (OUT7)
unnamed: LED89.1 (K), U6.13 (OUT8)
unnamed: LED90.1 (K), U6.14 (OUT9)
unnamed: LED91.1 (K), U6.15 (OUT10)
unnamed: LED92.1 (K), U6.16 (OUT11)
unnamed: LED93.1 (K), U6.17 (OUT12)
unnamed: LED94.1 (K), U6.18 (OUT13)
unnamed: LED95.1 (K), U6.19 (OUT14)
unnamed: LED96.1 (K), U6.20 (OUT15)
unnamed: LED97.1 (K), U7.5 (OUT0)
unnamed: LED98.1 (K), U7.6 (OUT1)
unnamed: LED99.1 (K), U7.7 (OUT2)
unnamed: LED100.1 (K), U7.8 (OUT3)
unnamed: LED101.1 (K), U7.9 (OUT4)
unnamed: LED102.1 (K), U7.10 (OUT5)
unnamed: LED103.1 (K), U7.11 (OUT6)
unnamed: LED104.1 (K), U7.12 (OUT7)
unnamed: LED105.1 (K), U7.13 (OUT8)
unnamed: LED106.1 (K), U7.14 (OUT9)
unnamed: LED107.1 (K), U7.15 (OUT10)
unnamed: LED108.1 (K), U7.16 (OUT11)
unnamed: LED109.1 (K), U7.17 (OUT12)
unnamed: LED110.1 (K), U7.18 (OUT13)
unnamed: LED111.1 (K), U7.19 (OUT14)
unnamed: LED112.1 (K), U7.20 (OUT15)
unnamed: LED113.1 (K), U8.5 (OUT0)
unnamed: LED114.1 (K), U8.6 (OUT1)
unnamed: LED115.1 (K), U8.7 (OUT2)
unnamed: LED116.1 (K), U8.8 (OUT3)
unnamed: LED117.1 (K), U8.9 (OUT4)
unnamed: LED118.1 (K), U8.10 (OUT5)
unnamed: LED119.1 (K), U8.11 (OUT6)
unnamed: LED120.1 (K), U8.12 (OUT7)
unnamed: LED121.1 (K), U8.13 (OUT8)
unnamed: LED122.1 (K), U8.14 (OUT9)
unnamed: LED123.1 (K), U8.15 (OUT10)
unnamed: LED124.1 (K), U8.16 (OUT11)
unnamed: LED125.1 (K), U8.17 (OUT12)
unnamed: LED126.1 (K), U8.18 (OUT13)
unnamed: LED127.1 (K), U8.19 (OUT14)
unnamed: LED128.1 (K), U8.20 (OUT15)
unnamed: LED129.1 (K), U9.5 (OUT0)
unnamed: LED130.1 (K), U9.6 (OUT1)
unnamed: LED131.1 (K), U9.7 (OUT2)
unnamed: LED132.1 (K), U9.8 (OUT3)
unnamed: LED133.1 (K), U9.9 (OUT4)
unnamed: LED134.1 (K), U9.10 (OUT5)
unnamed: LED135.1 (K), U9.11 (OUT6)
unnamed: LED136.1 (K), U9.12 (OUT7)
unnamed: LED137.1 (K), U9.13 (OUT8)
unnamed: LED138.1 (K), U9.14 (OUT9)
unnamed: LED139.1 (K), U9.15 (OUT10)
unnamed: LED140.1 (K), U9.16 (OUT11)
unnamed: LED141.1 (K), U9.17 (OUT12)
unnamed: LED142.1 (K), U9.18 (OUT13)
unnamed: LED143.1 (K), U9.19 (OUT14)
unnamed: LED144.1 (K), U9.20 (OUT15)
unnamed: LED145.1 (K), U10.5 (OUT0)
unnamed: LED146.1 (K), U10.6 (OUT1)
unnamed: LED147.1 (K), U10.7 (OUT2)
unnamed: LED148.1 (K), U10.8 (OUT3)
unnamed: LED149.1 (K), U10.9 (OUT4)
unnamed: LED150.1 (K), U10.10 (OUT5)
unnamed: LED151.1 (K), U10.11 (OUT6)
unnamed: LED152.1 (K), U10.12 (OUT7)
unnamed: LED153.1 (K), U10.13 (OUT8)
unnamed: LED154.1 (K), U10.14 (OUT9)
unnamed: LED155.1 (K), U10.15 (OUT10)
unnamed: LED156.1 (K), U10.16 (OUT11)
unnamed: LED157.1 (K), U10.17 (OUT12)
unnamed: LED158.1 (K), U10.18 (OUT13)
unnamed: LED159.1 (K), U10.19 (OUT14)
unnamed: LED160.1 (K), U10.20 (OUT15)
unnamed: LED161.1 (K), U11.5 (OUT0)
unnamed: LED162.1 (K), U11.6 (OUT1)
unnamed: LED163.1 (K), U11.7 (OUT2)
unnamed: LED164.1 (K), U11.8 (OUT3)
unnamed: LED165.1 (K), U11.9 (OUT4)
unnamed: LED166.1 (K), U11.10 (OUT5)
unnamed: LED167.1 (K), U11.11 (OUT6)
unnamed: LED168.1 (K), U11.12 (OUT7)
unnamed: LED169.1 (K), U11.13 (OUT8)
unnamed: LED170.1 (K), U11.14 (OUT9)
unnamed: LED171.1 (K), U11.15 (OUT10)
unnamed: LED172.1 (K), U11.16 (OUT11)
unnamed: LED173.1 (K), U11.17 (OUT12)
unnamed: LED174.1 (K), U11.18 (OUT13)
unnamed: LED175.1 (K), U11.19 (OUT14)
unnamed: LED176.1 (K), U11.20 (OUT15)
unnamed: LED177.1 (K), U12.5 (OUT0)
unnamed: LED178.1 (K), U12.6 (OUT1)
unnamed: LED179.1 (K), U12.7 (OUT2)
unnamed: LED180.1 (K), U12.8 (OUT3)
unnamed: LED181.1 (K), U12.9 (OUT4)
unnamed: LED182.1 (K), U12.10 (OUT5)
unnamed: LED183.1 (K), U12.11 (OUT6)
unnamed: LED184.1 (K), U12.12 (OUT7)
unnamed: LED185.1 (K), U12.13 (OUT8)
unnamed: LED186.1 (K), U12.14 (OUT9)
unnamed: LED187.1 (K), U12.15 (OUT10)
unnamed: LED188.1 (K), U12.16 (OUT11)
unnamed: LED189.1 (K), U12.17 (OUT12)
unnamed: LED190.1 (K), U12.18 (OUT13)
unnamed: LED191.1 (K), U12.19 (OUT14)
unnamed: LED192.1 (K), U12.20 (OUT15)
unnamed: LED193.1 (K), U13.5 (OUT0)
unnamed: LED194.1 (K), U13.6 (OUT1)
unnamed: LED195.1 (K), U13.7 (OUT2)
unnamed: LED196.1 (K), U13.8 (OUT3)
unnamed: LED197.1 (K), U13.9 (OUT4)
unnamed: LED198.1 (K), U13.10 (OUT5)
unnamed: LED199.1 (K), U13.11 (OUT6)
unnamed: LED200.1 (K), U13.12 (OUT7)
unnamed: LED201.1 (K), U13.13 (OUT8)
unnamed: LED202.1 (K), U13.14 (OUT9)
unnamed: LED203.1 (K), U13.15 (OUT10)
unnamed: LED204.1 (K), U13.16 (OUT11)
unnamed: LED205.1 (K), U13.17 (OUT12)
unnamed: LED206.1 (K), U13.18 (OUT13)
unnamed: LED207.1 (K), U13.19 (OUT14)
unnamed: LED208.1 (K), U13.20 (OUT15)
unnamed: LED209.1 (K), U14.5 (OUT0)
unnamed: LED210.1 (K), U14.6 (OUT1)
unnamed: LED211.1 (K), U14.7 (OUT2)
unnamed: LED212.1 (K), U14.8 (OUT3)
unnamed: LED213.1 (K), U14.9 (OUT4)
unnamed: LED214.1 (K), U14.10 (OUT5)
unnamed: LED215.1 (K), U14.11 (OUT6)
unnamed: LED216.1 (K), U14.12 (OUT7)
unnamed: LED217.1 (K), U14.13 (OUT8)
unnamed: LED218.1 (K), U14.14 (OUT9)
unnamed: LED219.1 (K), U14.15 (OUT10)
unnamed: LED220.1 (K), U14.16 (OUT11)
unnamed: LED221.1 (K), U14.17 (OUT12)
unnamed: LED222.1 (K), U14.18 (OUT13)
unnamed: LED223.1 (K), U14.19 (OUT14)
unnamed: LED224.1 (K), U14.20 (OUT15)
unnamed: LED225.1 (K), U15.5 (OUT0)
unnamed: LED226.1 (K), U15.6 (OUT1)
unnamed: LED227.1 (K), U15.7 (OUT2)
unnamed: LED228.1 (K), U15.8 (OUT3)
unnamed: LED229.1 (K), U15.9 (OUT4)
unnamed: LED230.1 (K), U15.10 (OUT5)
unnamed: LED231.1 (K), U15.11 (OUT6)
unnamed: LED232.1 (K), U15.12 (OUT7)
unnamed: LED233.1 (K), U15.13 (OUT8)
unnamed: LED234.1 (K), U15.14 (OUT9)
unnamed: LED235.1 (K), U15.15 (OUT10)
unnamed: LED236.1 (K), U15.16 (OUT11)
unnamed: LED237.1 (K), U15.17 (OUT12)
unnamed: LED238.1 (K), U15.18 (OUT13)
unnamed: LED239.1 (K), U15.19 (OUT14)
unnamed: LED240.1 (K), U15.20 (OUT15)
unnamed: LED241.1 (K), U16.5 (OUT0)
unnamed: LED242.1 (K), U16.6 (OUT1)
unnamed: LED243.1 (K), U16.7 (OUT2)
unnamed: LED244.1 (K), U16.8 (OUT3)
unnamed: LED245.1 (K), U16.9 (OUT4)
unnamed: LED246.1 (K), U16.10 (OUT5)
unnamed: LED247.1 (K), U16.11 (OUT6)
unnamed: LED248.1 (K), U16.12 (OUT7)
unnamed: LED249.1 (K), U16.13 (OUT8)
unnamed: LED250.1 (K), U16.14 (OUT9)
unnamed: LED251.1 (K), U16.15 (OUT10)
unnamed: LED252.1 (K), U16.16 (OUT11)
unnamed: LED253.1 (K), U16.17 (OUT12)
unnamed: LED254.1 (K), U16.18 (OUT13)
unnamed: LED255.1 (K), U16.19 (OUT14)
unnamed: LED256.1 (K), U16.20 (OUT15)
unnamed: LED257.1 (K), U17.5 (OUT0)
unnamed: LED258.1 (K), U17.6 (OUT1)
unnamed: LED259.1 (K), U17.7 (OUT2)
unnamed: LED260.1 (K), U17.8 (OUT3)
unnamed: LED261.1 (K), U17.9 (OUT4)
unnamed: LED262.1 (K), U17.10 (OUT5)
unnamed: LED263.1 (K), U17.11 (OUT6)
unnamed: LED264.1 (K), U17.12 (OUT7)
unnamed: LED265.1 (K), U17.13 (OUT8)
unnamed: LED266.1 (K), U17.14 (OUT9)
unnamed: LED267.1 (K), U17.15 (OUT10)
unnamed: LED268.1 (K), U17.16 (OUT11)
unnamed: LED269.1 (K), U17.17 (OUT12)
unnamed: LED270.1 (K), U17.18 (OUT13)
unnamed: LED271.1 (K), U17.19 (OUT14)
unnamed: LED272.1 (K), U17.20 (OUT15)
unnamed: LED273.1 (K), U18.5 (OUT0)
unnamed: LED274.1 (K), U18.6 (OUT1)
unnamed: LED275.1 (K), U18.7 (OUT2)
unnamed: LED276.1 (K), U18.8 (OUT3)
unnamed: LED277.1 (K), U18.9 (OUT4)
unnamed: LED278.1 (K), U18.10 (OUT5)
unnamed: LED279.1 (K), U18.11 (OUT6)
unnamed: LED280.1 (K), U18.12 (OUT7)
unnamed: LED281.1 (K), U18.13 (OUT8)
unnamed: LED282.1 (K), U18.14 (OUT9)
unnamed: LED283.1 (K), U18.15 (OUT10)
unnamed: LED284.1 (K), U18.16 (OUT11)
unnamed: LED285.1 (K), U18.17 (OUT12)
unnamed: LED286.1 (K), U18.18 (OUT13)
unnamed: LED287.1 (K), U18.19 (OUT14)
unnamed: LED288.1 (K), U18.20 (OUT15)
unnamed: LED289.1 (K), U19.5 (OUT0)
unnamed: LED290.1 (K), U19.6 (OUT1)
unnamed: LED291.1 (K), U19.7 (OUT2)
unnamed: LED292.1 (K), U19.8 (OUT3)
unnamed: LED293.1 (K), U19.9 (OUT4)
unnamed: LED294.1 (K), U19.10 (OUT5)
unnamed: LED295.1 (K), U19.11 (OUT6)
unnamed: LED296.1 (K), U19.12 (OUT7)
unnamed: LED297.1 (K), U19.13 (OUT8)
unnamed: LED298.1 (K), U19.14 (OUT9)
unnamed: LED299.1 (K), U19.15 (OUT10)
unnamed: LED300.1 (K), U19.16 (OUT11)
unnamed: LED301.1 (K), U19.17 (OUT12)
unnamed: LED302.1 (K), U19.18 (OUT13)
unnamed: LED303.1 (K), U19.19 (OUT14)
unnamed: LED304.1 (K), U19.20 (OUT15)
unnamed: LED305.1 (K), U20.5 (OUT0)
unnamed: LED306.1 (K), U20.6 (OUT1)
unnamed: LED307.1 (K), U20.7 (OUT2)
unnamed: LED308.1 (K), U20.8 (OUT3)
unnamed: LED309.1 (K), U20.9 (OUT4)
unnamed: LED310.1 (K), U20.10 (OUT5)
unnamed: LED311.1 (K), U20.11 (OUT6)
unnamed: LED312.1 (K), U20.12 (OUT7)
unnamed: LED313.1 (K), U20.13 (OUT8)
unnamed: LED314.1 (K), U20.14 (OUT9)
unnamed: LED315.1 (K), U20.15 (OUT10)
unnamed: LED316.1 (K), U20.16 (OUT11)
unnamed: LED317.1 (K), U20.17 (OUT12)
unnamed: LED318.1 (K), U20.18 (OUT13)
unnamed: LED319.1 (K), U20.19 (OUT14)
unnamed: LED320.1 (K), U20.20 (OUT15)
unnamed: LED321.1 (K), U21.5 (OUT0)
unnamed: LED322.1 (K), U21.6 (OUT1)
unnamed: LED323.1 (K), U21.7 (OUT2)
unnamed: LED324.1 (K), U21.8 (OUT3)
unnamed: LED325.1 (K), U21.9 (OUT4)
unnamed: LED326.1 (K), U21.10 (OUT5)
unnamed: LED327.1 (K), U21.11 (OUT6)
unnamed: LED328.1 (K), U21.12 (OUT7)
unnamed: LED329.1 (K), U21.13 (OUT8)
unnamed: LED330.1 (K), U21.14 (OUT9)
unnamed: LED331.1 (K), U21.15 (OUT10)
unnamed: LED332.1 (K), U21.16 (OUT11)
unnamed: LED333.1 (K), U21.17 (OUT12)
unnamed: LED334.1 (K), U21.18 (OUT13)
unnamed: LED335.1 (K), U21.19 (OUT14)
unnamed: LED336.1 (K), U21.20 (OUT15)
unnamed: LED337.1 (K), U22.5 (OUT0)
unnamed: LED338.1 (K), U22.6 (OUT1)
unnamed: LED339.1 (K), U22.7 (OUT2)
unnamed: LED340.1 (K), U22.8 (OUT3)
unnamed: LED341.1 (K), U22.9 (OUT4)
unnamed: LED342.1 (K), U22.10 (OUT5)
unnamed: LED343.1 (K), U22.11 (OUT6)
unnamed: LED344.1 (K), U22.12 (OUT7)
unnamed: LED345.1 (K), U22.13 (OUT8)
unnamed: LED346.1 (K), U22.14 (OUT9)
unnamed: LED347.1 (K), U22.15 (OUT10)
unnamed: LED348.1 (K), U22.16 (OUT11)
unnamed: LED349.1 (K), U22.17 (OUT12)
unnamed: LED350.1 (K), U22.18 (OUT13)
unnamed: LED351.1 (K), U22.19 (OUT14)
unnamed: LED352.1 (K), U22.20 (OUT15)
unnamed: LED353.1 (K), U23.5 (OUT0)
unnamed: LED354.1 (K), U23.6 (OUT1)
unnamed: LED355.1 (K), U23.7 (OUT2)
unnamed: LED356.1 (K), U23.8 (OUT3)
unnamed: LED357.1 (K), U23.9 (OUT4)
unnamed: LED358.1 (K), U23.10 (OUT5)
unnamed: LED359.1 (K), U23.11 (OUT6)
unnamed: LED360.1 (K), U23.12 (OUT7)
unnamed: LED361.1 (K), U23.13 (OUT8)
unnamed: LED362.1 (K), U23.14 (OUT9)
unnamed: LED363.1 (K), U23.15 (OUT10)
unnamed: LED364.1 (K), U23.16 (OUT11)
unnamed: LED365.1 (K), U23.17 (OUT12)
unnamed: LED366.1 (K), U23.18 (OUT13)
unnamed: LED367.1 (K), U23.19 (OUT14)
unnamed: LED368.1 (K), U23.20 (OUT15)
unnamed: LED369.1 (K), U24.5 (OUT0)
unnamed: LED370.1 (K), U24.6 (OUT1)
unnamed: LED371.1 (K), U24.7 (OUT2)
unnamed: LED372.1 (K), U24.8 (OUT3)
unnamed: LED373.1 (K), U24.9 (OUT4)
unnamed: LED374.1 (K), U24.10 (OUT5)
unnamed: LED375.1 (K), U24.11 (OUT6)
unnamed: LED376.1 (K), U24.12 (OUT7)
unnamed: LED377.1 (K), U24.13 (OUT8)
unnamed: LED378.1 (K), U24.14 (OUT9)
unnamed: LED379.1 (K), U24.15 (OUT10)
unnamed: LED380.1 (K), U24.16 (OUT11)
unnamed: LED381.1 (K), U24.17 (OUT12)
unnamed: LED382.1 (K), U24.18 (OUT13)
unnamed: LED383.1 (K), U24.19 (OUT14)
unnamed: LED384.1 (K), U24.20 (OUT15)
unnamed: LED385.1 (K), U25.5 (OUT0)
unnamed: LED386.1 (K), U25.6 (OUT1)
unnamed: LED387.1 (K), U25.7 (OUT2)
unnamed: LED388.1 (K), U25.8 (OUT3)
unnamed: LED389.1 (K), U25.9 (OUT4)
unnamed: LED390.1 (K), U25.10 (OUT5)
unnamed: LED391.1 (K), U25.11 (OUT6)
unnamed: LED392.1 (K), U25.12 (OUT7)
unnamed: LED393.1 (K), U25.13 (OUT8)
unnamed: LED394.1 (K), U25.14 (OUT9)
unnamed: LED395.1 (K), U25.15 (OUT10)
unnamed: LED396.1 (K), U25.16 (OUT11)
unnamed: LED397.1 (K), U25.17 (OUT12)
unnamed: LED398.1 (K), U25.18 (OUT13)
unnamed: LED399.1 (K), U25.19 (OUT14)
unnamed: LED400.1 (K), U25.20 (OUT15)
unnamed: LED401.1 (K), U26.5 (OUT0)
unnamed: LED402.1 (K), U26.6 (OUT1)
unnamed: LED403.1 (K), U26.7 (OUT2)
unnamed: LED404.1 (K), U26.8 (OUT3)
unnamed: LED405.1 (K), U26.9 (OUT4)
unnamed: LED406.1 (K), U26.10 (OUT5)
unnamed: LED407.1 (K), U26.11 (OUT6)
unnamed: LED408.1 (K), U26.12 (OUT7)
unnamed: LED409.1 (K), U26.13 (OUT8)
unnamed: LED410.1 (K), U26.14 (OUT9)
unnamed: LED411.1 (K), U26.15 (OUT10)
unnamed: LED412.1 (K), U26.16 (OUT11)
unnamed: LED413.1 (K), U26.17 (OUT12)
unnamed: LED414.1 (K), U26.18 (OUT13)
unnamed: LED415.1 (K), U26.19 (OUT14)
unnamed: LED416.1 (K), U26.20 (OUT15)
unnamed: LED417.1 (K), U27.5 (OUT0)
unnamed: LED418.1 (K), U27.6 (OUT1)
unnamed: LED419.1 (K), U27.7 (OUT2)
unnamed: LED420.1 (K), U27.8 (OUT3)
unnamed: LED421.1 (K), U27.9 (OUT4)
unnamed: LED422.1 (K), U27.10 (OUT5)
unnamed: LED423.1 (K), U27.11 (OUT6)
unnamed: LED424.1 (K), U27.12 (OUT7)
unnamed: LED425.1 (K), U27.13 (OUT8)
unnamed: LED426.1 (K), U27.14 (OUT9)
unnamed: LED427.1 (K), U27.15 (OUT10)
unnamed: LED428.1 (K), U27.16 (OUT11)
unnamed: LED429.1 (K), U27.17 (OUT12)
unnamed: LED430.1 (K), U27.18 (OUT13)
unnamed: LED431.1 (K), U27.19 (OUT14)
unnamed: LED432.1 (K), U27.20 (OUT15)
unnamed: LED433.1 (K), U28.5 (OUT0)
unnamed: LED434.1 (K), U28.6 (OUT1)
unnamed: LED435.1 (K), U28.7 (OUT2)
unnamed: LED436.1 (K), U28.8 (OUT3)
unnamed: LED437.1 (K), U28.9 (OUT4)
unnamed: LED438.1 (K), U28.10 (OUT5)
unnamed: LED439.1 (K), U28.11 (OUT6)
unnamed: LED440.1 (K), U28.12 (OUT7)
unnamed: LED441.1 (K), U28.13 (OUT8)
unnamed: LED442.1 (K), U28.14 (OUT9)
unnamed: LED443.1 (K), U28.15 (OUT10)
unnamed: LED444.1 (K), U28.16 (OUT11)
unnamed: LED445.1 (K), U28.17 (OUT12)
unnamed: LED446.1 (K), U28.18 (OUT13)
unnamed: LED447.1 (K), U28.19 (OUT14)
unnamed: LED448.1 (K), U28.20 (OUT15)
unnamed: LED449.1 (K), U29.5 (OUT0)
unnamed: LED450.1 (K), U29.6 (OUT1)
unnamed: LED451.1 (K), U29.7 (OUT2)
unnamed: LED452.1 (K), U29.8 (OUT3)
unnamed: LED453.1 (K), U29.9 (OUT4)
unnamed: LED454.1 (K), U29.10 (OUT5)
unnamed: LED455.1 (K), U29.11 (OUT6)
unnamed: LED456.1 (K), U29.12 (OUT7)
unnamed: LED457.1 (K), U29.13 (OUT8)
unnamed: LED458.1 (K), U29.14 (OUT9)
unnamed: LED459.1 (K), U29.15 (OUT10)
unnamed: LED460.1 (K), U29.16 (OUT11)
unnamed: LED461.1 (K), U29.17 (OUT12)
unnamed: LED462.1 (K), U29.18 (OUT13)
unnamed: LED463.1 (K), U29.19 (OUT14)
unnamed: LED464.1 (K), U29.20 (OUT15)
unnamed: LED465.1 (K), U30.5 (OUT0)
unnamed: LED466.1 (K), U30.6 (OUT1)
unnamed: LED467.1 (K), U30.7 (OUT2)
unnamed: LED468.1 (K), U30.8 (OUT3)
unnamed: LED469.1 (K), U30.9 (OUT4)
unnamed: LED470.1 (K), U30.10 (OUT5)
unnamed: LED471.1 (K), U30.11 (OUT6)
unnamed: LED472.1 (K), U30.12 (OUT7)
unnamed: LED473.1 (K), U30.13 (OUT8)
unnamed: LED474.1 (K), U30.14 (OUT9)
unnamed: LED475.1 (K), U30.15 (OUT10)
unnamed: LED476.1 (K), U30.16 (OUT11)
unnamed: LED477.1 (K), U30.17 (OUT12)
unnamed: LED478.1 (K), U30.18 (OUT13)
unnamed: LED479.1 (K), U30.19 (OUT14)
unnamed: LED480.1 (K), U30.20 (OUT15)
unnamed: LED481.1 (K), U31.5 (OUT0)
unnamed: LED482.1 (K), U31.6 (OUT1)
unnamed: LED483.1 (K), U31.7 (OUT2)
unnamed: LED484.1 (K), U31.8 (OUT3)
unnamed: LED485.1 (K), U31.9 (OUT4)
unnamed: LED486.1 (K), U31.10 (OUT5)
unnamed: LED487.1 (K), U31.11 (OUT6)
unnamed: LED488.1 (K), U31.12 (OUT7)
unnamed: LED489.1 (K), U31.13 (OUT8)
unnamed: LED490.1 (K), U31.14 (OUT9)
unnamed: LED491.1 (K), U31.15 (OUT10)
unnamed: LED492.1 (K), U31.16 (OUT11)
unnamed: LED493.1 (K), U31.17 (OUT12)
unnamed: LED494.1 (K), U31.18 (OUT13)
unnamed: LED495.1 (K), U31.19 (OUT14)
unnamed: LED496.1 (K), U31.20 (OUT15)
unnamed: LED497.1 (K), U32.5 (OUT0)
unnamed: LED498.1 (K), U32.6 (OUT1)
unnamed: LED499.1 (K), U32.7 (OUT2)
unnamed: LED500.1 (K), U32.8 (OUT3)
unnamed: LED501.1 (K), U32.9 (OUT4)
unnamed: LED502.1 (K), U32.10 (OUT5)
unnamed: LED503.1 (K), U32.11 (OUT6)
unnamed: LED504.1 (K), U32.12 (OUT7)
unnamed: LED505.1 (K), U32.13 (OUT8)
unnamed: LED506.1 (K), U32.14 (OUT9)
unnamed: LED507.1 (K), U32.15 (OUT10)
unnamed: LED508.1 (K), U32.16 (OUT11)
unnamed: LED509.1 (K), U32.17 (OUT12)
unnamed: LED510.1 (K), U32.18 (OUT13)
unnamed: LED511.1 (K), U32.19 (OUT14)
unnamed: LED512.1 (K), U32.20 (OUT15)
unnamed: R1.2, U1.23 (R-EXT)
unnamed: R2.2, U2.23 (R-EXT)
unnamed: R3.2, U3.23 (R-EXT)
unnamed: R4.2, U4.23 (R-EXT)
unnamed: R5.2, U5.23 (R-EXT)
unnamed: R6.2, U6.23 (R-EXT)
unnamed: R7.2, U7.23 (R-EXT)
unnamed: R8.2, U8.23 (R-EXT)
unnamed: R9.2, U9.23 (R-EXT)
unnamed: R10.2, U10.23 (R-EXT)
unnamed: R11.2, U11.23 (R-EXT)
unnamed: R12.2, U12.23 (R-EXT)
unnamed: R13.2, U13.23 (R-EXT)
unnamed: R14.2, U14.23 (R-EXT)
unnamed: R15.2, U15.23 (R-EXT)
unnamed: R16.2, U16.23 (R-EXT)
unnamed: R17.2, U17.23 (R-EXT)
unnamed: R18.2, U18.23 (R-EXT)
unnamed: R19.2, U19.23 (R-EXT)
unnamed: R20.2, U20.23 (R-EXT)
unnamed: R21.2, U21.23 (R-EXT)
unnamed: R22.2, U22.23 (R-EXT)
unnamed: R23.2, U23.23 (R-EXT)
unnamed: R24.2, U24.23 (R-EXT)
unnamed: R25.2, U25.23 (R-EXT)
unnamed: R26.2, U26.23 (R-EXT)
unnamed: R27.2, U27.23 (R-EXT)
unnamed: R28.2, U28.23 (R-EXT)
unnamed: R29.2, U29.23 (R-EXT)
unnamed: R30.2, U30.23 (R-EXT)
unnamed: R31.2, U31.23 (R-EXT)
unnamed: R32.2, U32.23 (R-EXT)
unnamed: R33.1, U35.13 (SHELL), U35.14 (SHELL)
unnamed: R35.1, U35.4 (CC1_A5)
unnamed: R36.1, U35.10 (CC2_B5)
unnamed: R42.1, U33.4 (IO4)
unnamed: R43.1, U33.5 (IO5)
unnamed: R44.1, U33.6 (IO6)
unnamed: R45.1, U33.13 (IO19)
unnamed: R46.1, U33.14 (IO20)
unnamed: R48.2, R51.1, R56.2, U34.14 (FB)
unnamed: R49.2, U33.33 (IO40)
unnamed: R50.2, U33.32 (IO39)
unnamed: R52.2, U34.12 (MODE)
unnamed: R55.1, U33.17 (IO9)
unnamed: R57.1, U33.19 (IO11)
unnamed: R58.2, U36.11 (EN)
unnamed: R59.1, U33.20 (IO12)
unnamed: R60.1, U33.21 (IO13)
unnamed: R61.2, R62.1, U36.14 (FB)
unnamed: R63.1, R66.2, SW3.1 (A)
unnamed: R64.2, R65.1, SW4.1 (A)
unnamed: R65.2, U33.22 (IO14)
unnamed: R66.1, U33.23 (IO21)
SDO-01: U1.22 (SDO), U2.2 (SDI)
SDO-02: U2.22 (SDO), U3.2 (SDI)
SDO-03: U3.22 (SDO), U4.2 (SDI)
SDO-04: U4.22 (SDO), U5.2 (SDI)
SDO-05: U5.22 (SDO), U6.2 (SDI)
SDO-06: U6.22 (SDO), U7.2 (SDI)
SDO-07: U7.22 (SDO), U8.2 (SDI)
SDO-08: U8.22 (SDO), U9.2 (SDI)
SDO-09: U9.22 (SDO), U10.2 (SDI)
SDO-10: U10.22 (SDO), U11.2 (SDI)
SDO-11: U11.22 (SDO), U12.2 (SDI)
SDO-12: U12.22 (SDO), U13.2 (SDI)
SDO-13: U13.22 (SDO), U14.2 (SDI)
SDO-14: U14.22 (SDO), U15.2 (SDI)
SDO-15: U15.22 (SDO), U16.2 (SDI)
SDO-16: U16.22 (SDO), U17.2 (SDI)
SDO-17: U17.22 (SDO), U18.2 (SDI)
SDO-18: U18.22 (SDO), U19.2 (SDI)
SDO-19: U19.22 (SDO), U20.2 (SDI)
SDO-20: U20.22 (SDO), U21.2 (SDI)
SDO-21: U21.22 (SDO), U22.2 (SDI)
SDO-22: U22.22 (SDO), U23.2 (SDI)
SDO-23: U23.22 (SDO), U24.2 (SDI)
SDO-24: U24.22 (SDO), U25.2 (SDI)
SDO-25: U25.22 (SDO), U26.2 (SDI)
SDO-26: U26.22 (SDO), U27.2 (SDI)
SDO-27: U27.22 (SDO), U28.2 (SDI)
SDO-28: U28.22 (SDO), U29.2 (SDI)
SDO-29: U29.22 (SDO), U30.2 (SDI)
SDO-30: U30.22 (SDO), U31.2 (SDI)
SDO-31: U31.22 (SDO), U32.2 (SDI)
SW_Boot: C39.1, SW2.2, U33.27 (IO0)
SW_Reset: C35.1, C38.1, R34.2, SW1.2, U33.3 (EN)
USB_D+: D4.2 (A2), R46.2, U35.6 (DP1_A6), U35.8 (DP2_B6)
USB_D-: D3.2 (A2), R45.2, U35.5 (DN2_B7), U35.7 (DN1_A7)
VCC: C41.1, C42.1, C49.1, C50.1, C51.1, C52.1, C59.1, C65.1, C66.1, C67.1, J1.6, L1.2, LED1.2 (A), LED2.2 (A), LED3.2 (A), LED4.2 (A), LED5.2 (A), LED6.2 (A), LED7.2 (A), LED8.2 (A), LED9.2 (A), LED10.2 (A), LED11.2 (A), LED12.2 (A), LED13.2 (A), LED14.2 (A), LED15.2 (A), LED16.2 (A), LED17.2 (A), LED18.2 (A), LED19.2 (A), LED20.2 (A), LED21.2 (A), LED22.2 (A), LED23.2 (A), LED24.2 (A), LED25.2 (A), LED26.2 (A), LED27.2 (A), LED28.2 (A), LED29.2 (A), LED30.2 (A), LED31.2 (A), LED32.2 (A), LED33.2 (A), LED34.2 (A), LED35.2 (A), LED36.2 (A), LED37.2 (A), LED38.2 (A), LED39.2 (A), LED40.2 (A), LED41.2 (A), LED42.2 (A), LED43.2 (A), LED44.2 (A), LED45.2 (A), LED46.2 (A), LED47.2 (A), LED48.2 (A), LED49.2 (A), LED50.2 (A), LED51.2 (A), LED52.2 (A), LED53.2 (A), LED54.2 (A), LED55.2 (A), LED56.2 (A), LED57.2 (A), LED58.2 (A), LED59.2 (A), LED60.2 (A), LED61.2 (A), LED62.2 (A), LED63.2 (A), LED64.2 (A), LED65.2 (A), LED66.2 (A), LED67.2 (A), LED68.2 (A), LED69.2 (A), LED70.2 (A), LED71.2 (A), LED72.2 (A), LED73.2 (A), LED74.2 (A), LED75.2 (A), LED76.2 (A), LED77.2 (A), LED78.2 (A), LED79.2 (A), LED80.2 (A), LED81.2 (A), LED82.2 (A), LED83.2 (A), LED84.2 (A), LED85.2 (A), LED86.2 (A), LED87.2 (A), LED88.2 (A), LED89.2 (A), LED90.2 (A), LED91.2 (A), LED92.2 (A), LED93.2 (A), LED94.2 (A), LED95.2 (A), LED96.2 (A), LED97.2 (A), LED98.2 (A), LED99.2 (A), LED100.2 (A), LED101.2 (A), LED102.2 (A), LED103.2 (A), LED104.2 (A), LED105.2 (A), LED106.2 (A), LED107.2 (A), LED108.2 (A), LED109.2 (A), LED110.2 (A), LED111.2 (A), LED112.2 (A), LED113.2 (A), LED114.2 (A), LED115.2 (A), LED116.2 (A), LED117.2 (A), LED118.2 (A), LED119.2 (A), LED120.2 (A), LED121.2 (A), LED122.2 (A), LED123.2 (A), LED124.2 (A), LED125.2 (A), LED126.2 (A), LED127.2 (A), LED128.2 (A), LED129.2 (A), LED130.2 (A), LED131.2 (A), LED132.2 (A), LED133.2 (A), LED134.2 (A), LED135.2 (A), LED136.2 (A), LED137.2 (A), LED138.2 (A), LED139.2 (A), LED140.2 (A), LED141.2 (A), LED142.2 (A), LED143.2 (A), LED144.2 (A), LED145.2 (A), LED146.2 (A), LED147.2 (A), LED148.2 (A), LED149.2 (A), LED150.2 (A), LED151.2 (A), LED152.2 (A), LED153.2 (A), LED154.2 (A), LED155.2 (A), LED156.2 (A), LED157.2 (A), LED158.2 (A), LED159.2 (A), LED160.2 (A), LED161.2 (A), LED162.2 (A), LED163.2 (A), LED164.2 (A), LED165.2 (A), LED166.2 (A), LED167.2 (A), LED168.2 (A), LED169.2 (A), LED170.2 (A), LED171.2 (A), LED172.2 (A), LED173.2 (A), LED174.2 (A), LED175.2 (A), LED176.2 (A), LED177.2 (A), LED178.2 (A), LED179.2 (A), LED180.2 (A), LED181.2 (A), LED182.2 (A), LED183.2 (A), LED184.2 (A), LED185.2 (A), LED186.2 (A), LED187.2 (A), LED188.2 (A), LED189.2 (A), LED190.2 (A), LED191.2 (A), LED192.2 (A), LED193.2 (A), LED194.2 (A), LED195.2 (A), LED196.2 (A), LED197.2 (A), LED198.2 (A), LED199.2 (A), LED200.2 (A), LED201.2 (A), LED202.2 (A), LED203.2 (A), LED204.2 (A), LED205.2 (A), LED206.2 (A), LED207.2 (A), LED208.2 (A), LED209.2 (A), LED210.2 (A), LED211.2 (A), LED212.2 (A), LED213.2 (A), LED214.2 (A), LED215.2 (A), LED216.2 (A), LED217.2 (A), LED218.2 (A), LED219.2 (A), LED220.2 (A), LED221.2 (A), LED222.2 (A), LED223.2 (A), LED224.2 (A), LED225.2 (A), LED226.2 (A), LED227.2 (A), LED228.2 (A), LED229.2 (A), LED230.2 (A), LED231.2 (A), LED232.2 (A), LED233.2 (A), LED234.2 (A), LED235.2 (A), LED236.2 (A), LED237.2 (A), LED238.2 (A), LED239.2 (A), LED240.2 (A), LED241.2 (A), LED242.2 (A), LED243.2 (A), LED244.2 (A), LED245.2 (A), LED246.2 (A), LED247.2 (A), LED248.2 (A), LED249.2 (A), LED250.2 (A), LED251.2 (A), LED252.2 (A), LED253.2 (A), LED254.2 (A), LED255.2 (A), LED256.2 (A), LED257.2 (A), LED258.2 (A), LED259.2 (A), LED260.2 (A), LED261.2 (A), LED262.2 (A), LED263.2 (A), LED264.2 (A), LED265.2 (A), LED266.2 (A), LED267.2 (A), LED268.2 (A), LED269.2 (A), LED270.2 (A), LED271.2 (A), LED272.2 (A), LED273.2 (A), LED274.2 (A), LED275.2 (A), LED276.2 (A), LED277.2 (A), LED278.2 (A), LED279.2 (A), LED280.2 (A), LED281.2 (A), LED282.2 (A), LED283.2 (A), LED284.2 (A), LED285.2 (A), LED286.2 (A), LED287.2 (A), LED288.2 (A), LED289.2 (A), LED290.2 (A), LED291.2 (A), LED292.2 (A), LED293.2 (A), LED294.2 (A), LED295.2 (A), LED296.2 (A), LED297.2 (A), LED298.2 (A), LED299.2 (A), LED300.2 (A), LED301.2 (A), LED302.2 (A), LED303.2 (A), LED304.2 (A), LED305.2 (A), LED306.2 (A), LED307.2 (A), LED308.2 (A), LED309.2 (A), LED310.2 (A), LED311.2 (A), LED312.2 (A), LED313.2 (A), LED314.2 (A), LED315.2 (A), LED316.2 (A), LED317.2 (A), LED318.2 (A), LED319.2 (A), LED320.2 (A), LED321.2 (A), LED322.2 (A), LED323.2 (A), LED324.2 (A), LED325.2 (A), LED326.2 (A), LED327.2 (A), LED328.2 (A), LED329.2 (A), LED330.2 (A), LED331.2 (A), LED332.2 (A), LED333.2 (A), LED334.2 (A), LED335.2 (A), LED336.2 (A), LED337.2 (A), LED338.2 (A), LED339.2 (A), LED340.2 (A), LED341.2 (A), LED342.2 (A), LED343.2 (A), LED344.2 (A), LED345.2 (A), LED346.2 (A), LED347.2 (A), LED348.2 (A), LED349.2 (A), LED350.2 (A), LED351.2 (A), LED352.2 (A), LED353.2 (A), LED354.2 (A), LED355.2 (A), LED356.2 (A), LED357.2 (A), LED358.2 (A), LED359.2 (A), LED360.2 (A), LED361.2 (A), LED362.2 (A), LED363.2 (A), LED364.2 (A), LED365.2 (A), LED366.2 (A), LED367.2 (A), LED368.2 (A), LED369.2 (A), LED370.2 (A), LED371.2 (A), LED372.2 (A), LED373.2 (A), LED374.2 (A), LED375.2 (A), LED376.2 (A), LED377.2 (A), LED378.2 (A), LED379.2 (A), LED380.2 (A), LED381.2 (A), LED382.2 (A), LED383.2 (A), LED384.2 (A), LED385.2 (A), LED386.2 (A), LED387.2 (A), LED388.2 (A), LED389.2 (A), LED390.2 (A), LED391.2 (A), LED392.2 (A), LED393.2 (A), LED394.2 (A), LED395.2 (A), LED396.2 (A), LED397.2 (A), LED398.2 (A), LED399.2 (A), LED400.2 (A), LED401.2 (A), LED402.2 (A), LED403.2 (A), LED404.2 (A), LED405.2 (A), LED406.2 (A), LED407.2 (A), LED408.2 (A), LED409.2 (A), LED410.2 (A), LED411.2 (A), LED412.2 (A), LED413.2 (A), LED414.2 (A), LED415.2 (A), LED416.2 (A), LED417.2 (A), LED418.2 (A), LED419.2 (A), LED420.2 (A), LED421.2 (A), LED422.2 (A), LED423.2 (A), LED424.2 (A), LED425.2 (A), LED426.2 (A), LED427.2 (A), LED428.2 (A), LED429.2 (A), LED430.2 (A), LED431.2 (A), LED432.2 (A), LED433.2 (A), LED434.2 (A), LED435.2 (A), LED436.2 (A), LED437.2 (A), LED438.2 (A), LED439.2 (A), LED440.2 (A), LED441.2 (A), LED442.2 (A), LED443.2 (A), LED444.2 (A), LED445.2 (A), LED446.2 (A), LED447.2 (A), LED448.2 (A), LED449.2 (A), LED450.2 (A), LED451.2 (A), LED452.2 (A), LED453.2 (A), LED454.2 (A), LED455.2 (A), LED456.2 (A), LED457.2 (A), LED458.2 (A), LED459.2 (A), LED460.2 (A), LED461.2 (A), LED462.2 (A), LED463.2 (A), LED464.2 (A), LED465.2 (A), LED466.2 (A), LED467.2 (A), LED468.2 (A), LED469.2 (A), LED470.2 (A), LED471.2 (A), LED472.2 (A), LED473.2 (A), LED474.2 (A), LED475.2 (A), LED476.2 (A), LED477.2 (A), LED478.2 (A), LED479.2 (A), LED480.2 (A), LED481.2 (A), LED482.2 (A), LED483.2 (A), LED484.2 (A), LED485.2 (A), LED486.2 (A), LED487.2 (A), LED488.2 (A), LED489.2 (A), LED490.2 (A), LED491.2 (A), LED492.2 (A), LED493.2 (A), LED494.2 (A), LED495.2 (A), LED496.2 (A), LED497.2 (A), LED498.2 (A), LED499.2 (A), LED500.2 (A), LED501.2 (A), LED502.2 (A), LED503.2 (A), LED504.2 (A), LED505.2 (A), LED506.2 (A), LED507.2 (A), LED508.2 (A), LED509.2 (A), LED510.2 (A), LED511.2 (A), LED512.2 (A), R48.1
VDD: C1.1, C2.1, C3.1, C4.1, C5.1, C6.1, C7.1, C8.1, C9.1, C10.1, C11.1, C12.1, C13.1, C14.1, C15.1, C16.1, C17.1, C18.1, C19.1, C20.1, C21.1, C22.1, C23.1, C24.1, C25.1, C26.1, C27.1, C28.1, C29.1, C30.1, C31.1, C32.1, C33.1, C34.1, C45.1, C60.1, C61.1, C62.1, C63.1, C64.1, J1.5, L2.2, R34.1, R37.2, R38.2, R39.2, R41.1, R52.1, R54.1, R61.1, R63.2, R64.1, U33.2 (3V3), U34.15 (BYP)
buck4v_EN: R53.1, R55.2, U34.11 (EN)
buck4v_PG: C44.1, R54.2, U33.18 (IO10), U34.9 (PG)

Notes on the sheet:
Cin and Cout caps hould be at least X5R/X7R and at least 10v 1210
1 PWM 2 GND 3 V+ 4 Z 5 B 6 A
